axytho/FHEWHW/ThesisProjectGit/Papers/graphicsDM/oneTimePad.jpg

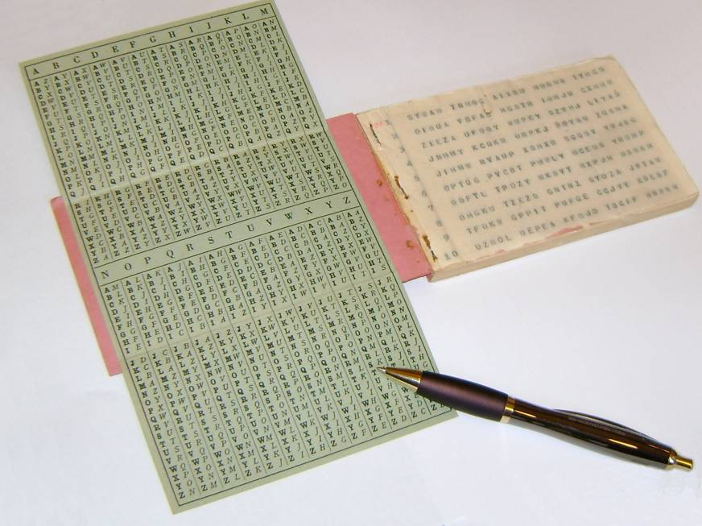
ThesisProjectGit/Papers/graphicsDM/oneTimePad.jpg
