axytho/FHEWHW/ThesisProjectGit/DraftPlanning.xlsx

 |  |  | E-mails updating the assistants are sent every week on Friday morning
 | Week | Summer holidays | Watching Simons institute lectures
1 | 39 | 2020-09-21 | Learning Microsoft SEAL
2 | 40 | 2020-09-28 | Microsoft SEAL program/ FV paper/ Pallisade lectures
3 | 41 | 2020-10-05 | FV Hardware implementation papers/ SEAL/Palisade
4 | 42 | 2020-10-12 | Further literature study and practice
5 | 43 | 2020-10-19 | Starting to work on the FPGA, learning how to program it
6 | 44 | 2020-10-26 | Literature study and decision on what to implement in hardware | Milestone: Decision on what to implement
7 | 45 | 2020-11-02 | Further literature study on scheme and start of implementation
8 | 46 | 2020-11-09 | Hardware implementation | Milestone: Planning of HW implementation and goals for different weeks
9 | 47 | 2020-11-16 | Hardware implementation
10 | 48 | 2020-11-23 | Hardware implementation
11 | 49 | 2020-11-30 | Hardware implementation
12 | 50 | 2020-12-07 | Hardware implementation
13 | 51 | 2020-12-14 | HW + Interim presentation
 | 52 | 2020-12-21 | INTERIM PRESENTATION DEADLINE | Milestone: Interim Presentation
 | 1 | 2020-12-28
 | 2 | 2021-01-04
 | 3 | 2021-01-11
 | 4 | 2021-01-18
 | 5 | 2021-01-25
 | 6 | 2021-02-01
14 | 7 | 2021-02-08 | Hardware implementation
15 | 8 | 2021-02-15 | Hardware implementation
16 | 9 | 2021-02-22 | Hardware implementation
17 | 10 | 2021-03-01 | Hardware implementation
18 | 11 | 2021-03-08 | Hardware implementation
19 | 12 | 2021-03-15 | Hardware implementation | Milestone: Finished HW implementation
20 | 13 | 2021-03-22 | Thesis write-up
21 | 14 | 2021-03-29 | Thesis write-up
22 | 15 | 2021-04-05 | Thesis write-up
23 | 16 | 2021-04-12 | Thesis write-up
24 | 17 | 2021-04-19 | Thesis write-up | Milestone: Finished Thesis
25 | 18 | 2021-04-26 | Article write-up
26 | 19 | 2021-05-03 | Article write-up | Milestone: Finished Article
 | 20 | 2021-05-10 | Further optimizations if possible and thesis write-up
 | 21 | 2021-05-17 | Further optimizations if possible and thesis write-up
 | 22 | 2021-05-24 | Further optimizations if possible and thesis write-up | Milestone: Thesis spell checked/ corrected and further optimizations done
 | 23 | 2021-05-31 | THESIS DEADLINE
 |  |  |  | Milestone: Final Presentation
