axytho/FHEWHW/ThesisProjectGit/2022Work/Capture.PNG

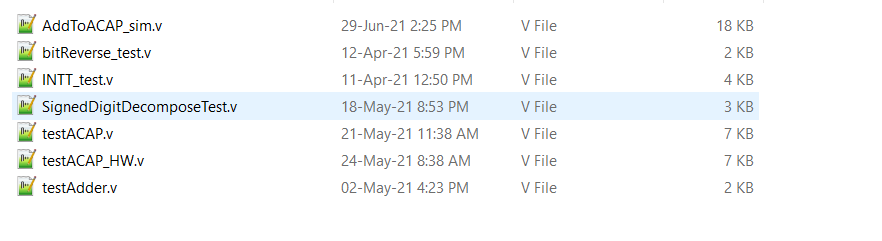
ThesisProjectGit/2022Work/Capture.PNG
