axytho/FHEWHW/ThesisProjectGit/blockDiagram/leftSide.PNG

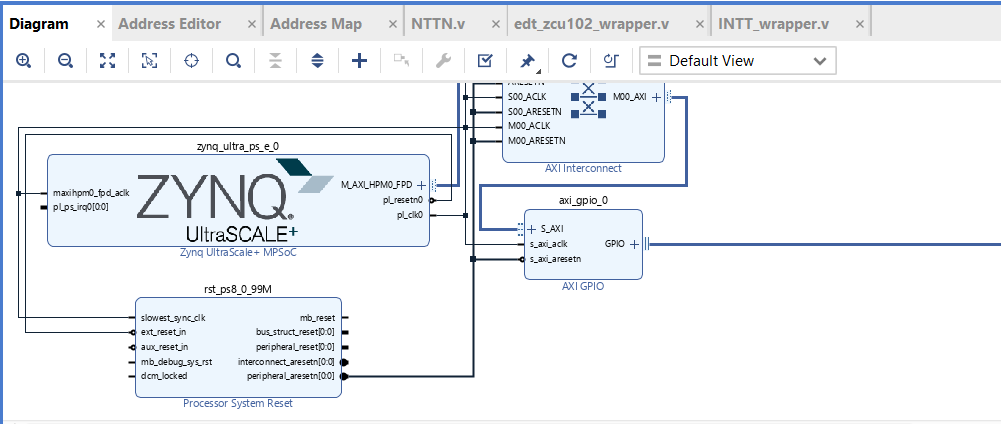
ThesisProjectGit/blockDiagram/leftSide.PNG
