axytho/FHEWHW/ThesisProjectGit/blockDiagram/RightSide.PNG

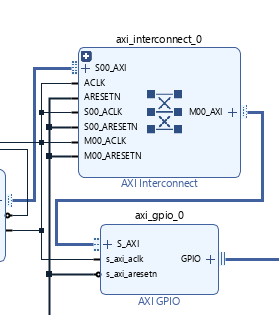
ThesisProjectGit/blockDiagram/RightSide.PNG
