axytho/FHEWHW/ThesisProjectGit/Papers/graphicsDM/Accumulation.PNG

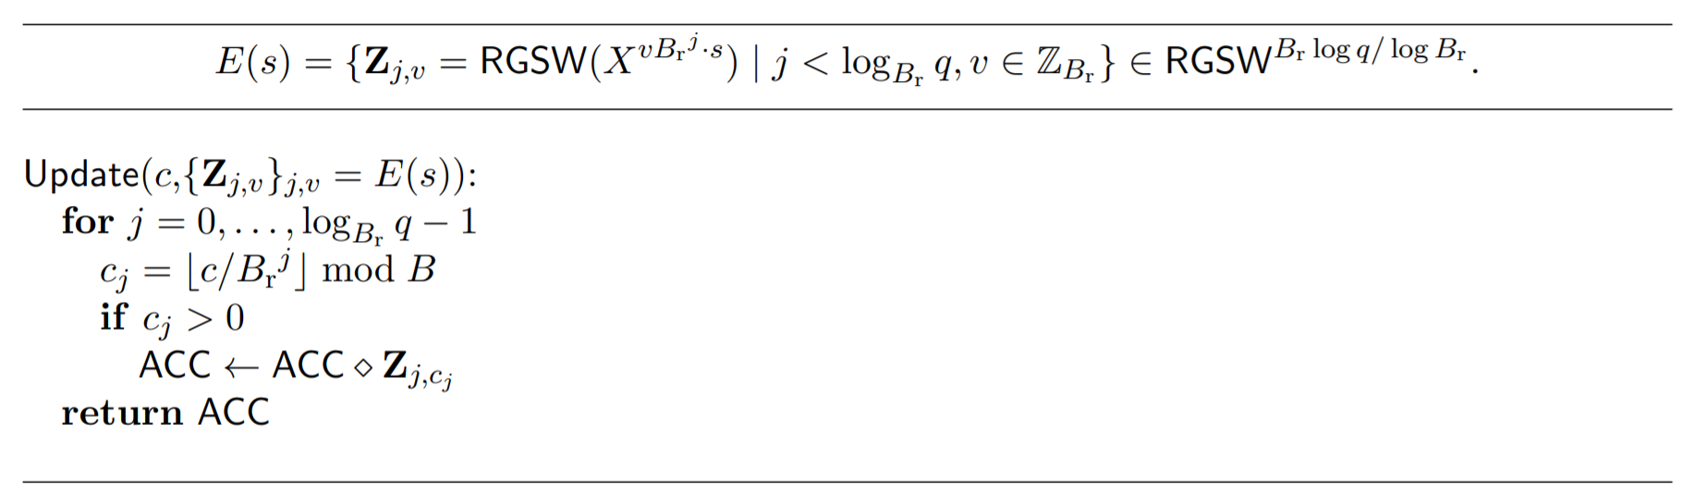
ThesisProjectGit/Papers/graphicsDM/Accumulation.PNG
