axytho/FHEWHW/ThesisProjectGit/Papers/graphicsDM/boxInsideABox.png

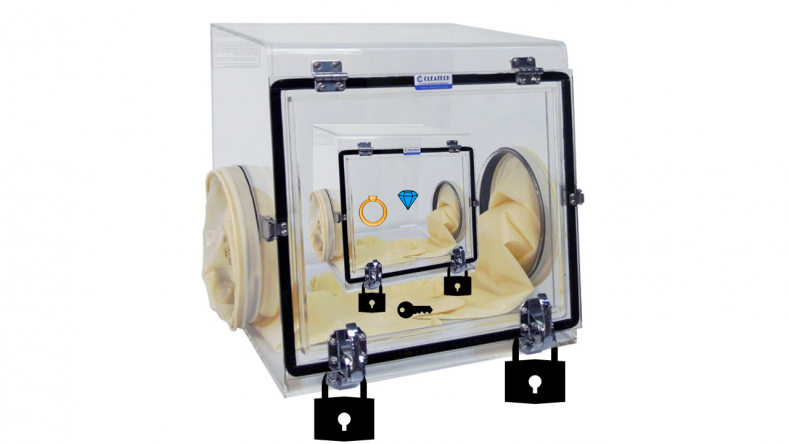
ThesisProjectGit/Papers/graphicsDM/boxInsideABox.png
