axytho/FHEWHW/ThesisProjectGit/Papers/graphicsDM/CooleyTukey.PNG

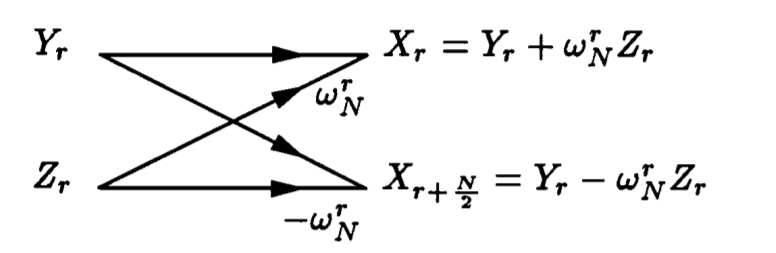
ThesisProjectGit/Papers/graphicsDM/CooleyTukey.PNG
