axytho/FHEWHW/ThesisProjectGit/Papers/graphicsDM/ElevenClockCycleBRAM.PNG

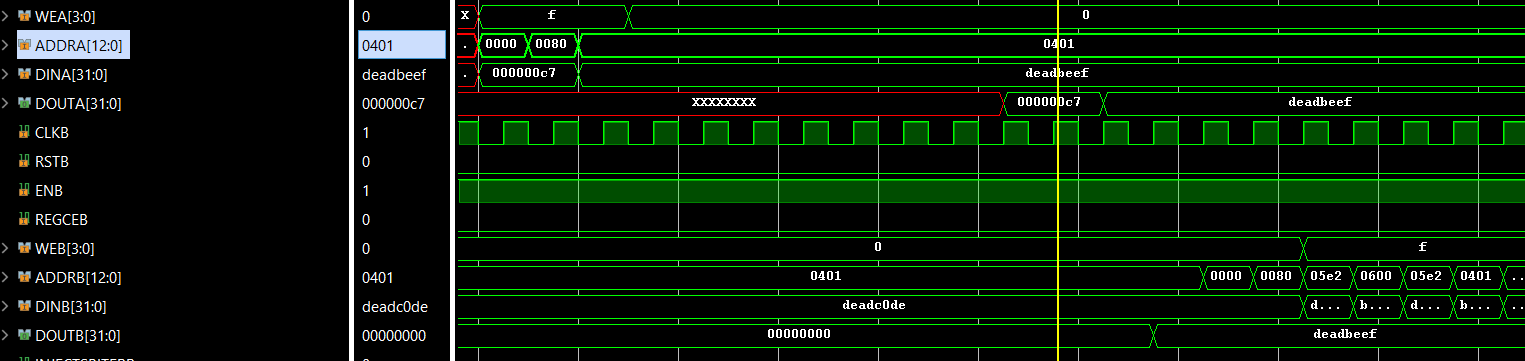
ThesisProjectGit/Papers/graphicsDM/ElevenClockCycleBRAM.PNG
