axytho/FHEWHW/ThesisProjectGit/Papers/graphicsDM/FHEWflowchart.png

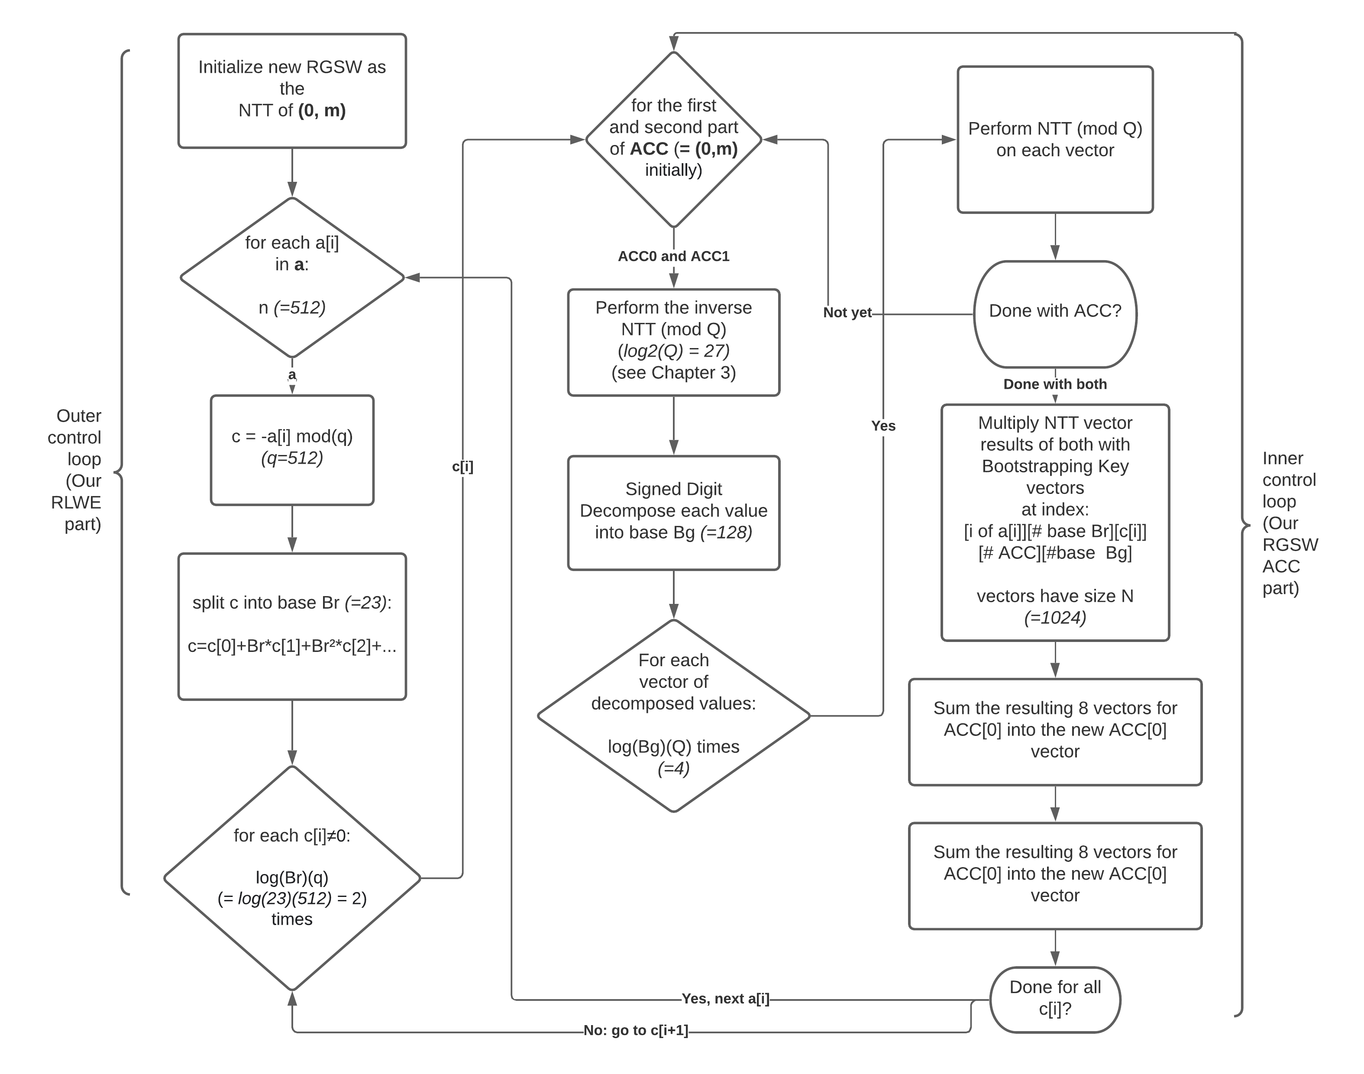
ThesisProjectGit/Papers/graphicsDM/FHEWflowchart.png
