axytho/FHEWHW/ThesisProjectGit/Papers/graphicsDM/GentlemanSande.PNG

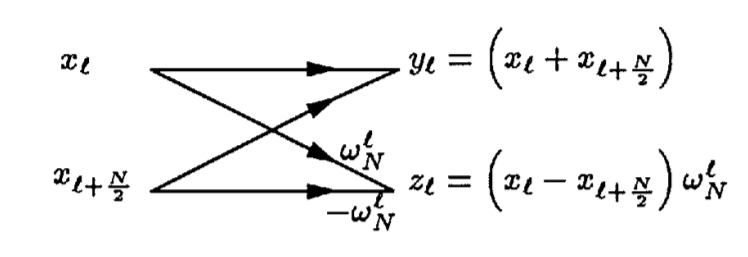
ThesisProjectGit/Papers/graphicsDM/GentlemanSande.PNG
