axytho/FHEWHW/ThesisProjectGit/Papers/graphicsDM/InitializationExtraction.PNG

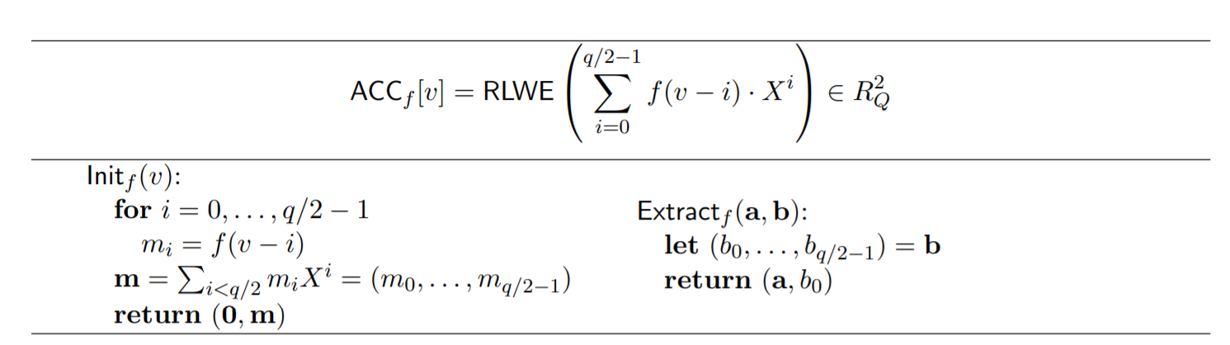
ThesisProjectGit/Papers/graphicsDM/InitializationExtraction.PNG
