axytho/FHEWHW/ThesisProjectGit/Papers/graphicsDM/MERTINTT.png

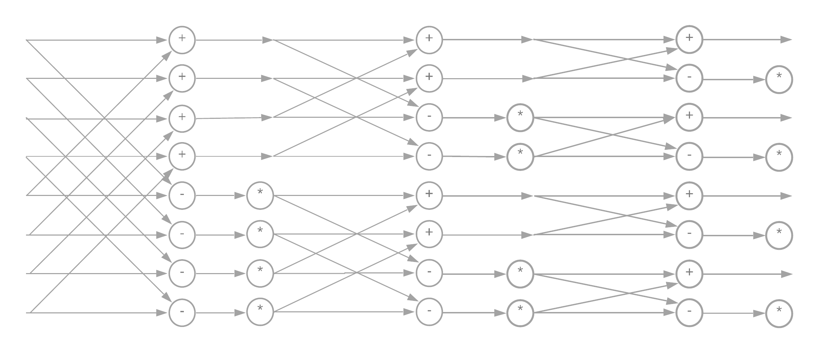
ThesisProjectGit/Papers/graphicsDM/MERTINTT.png
