axytho/FHEWHW/ThesisProjectGit/Papers/graphicsDM/Picture1.png

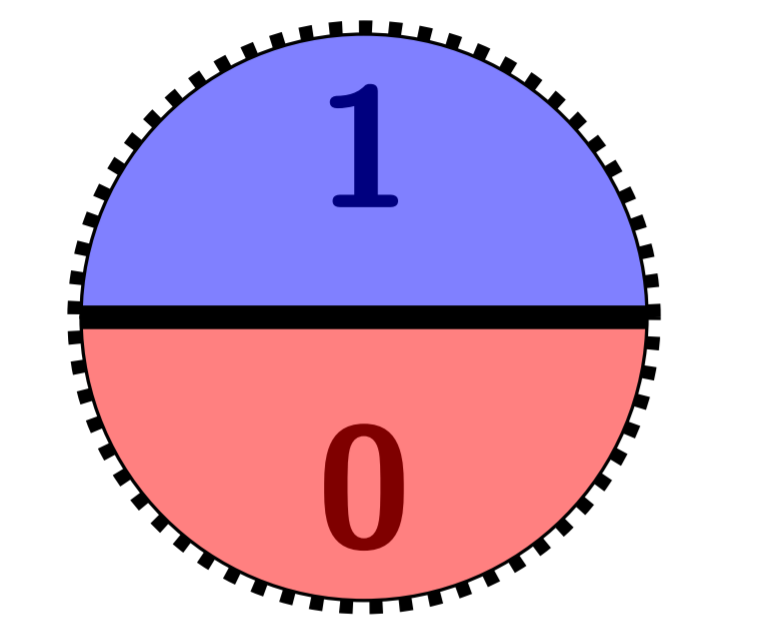
ThesisProjectGit/Papers/graphicsDM/Picture1.png
