axytho/FHEWHW/ThesisProjectGit/Papers/graphicsDM/Picture2.png

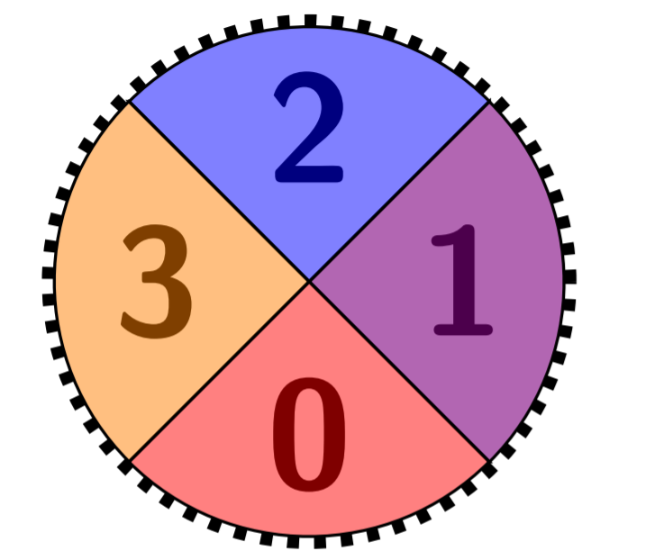
ThesisProjectGit/Papers/graphicsDM/Picture2.png
