axytho/FHEWHW/ThesisProjectGit/Papers/graphicsDM/Picture2half.PNG

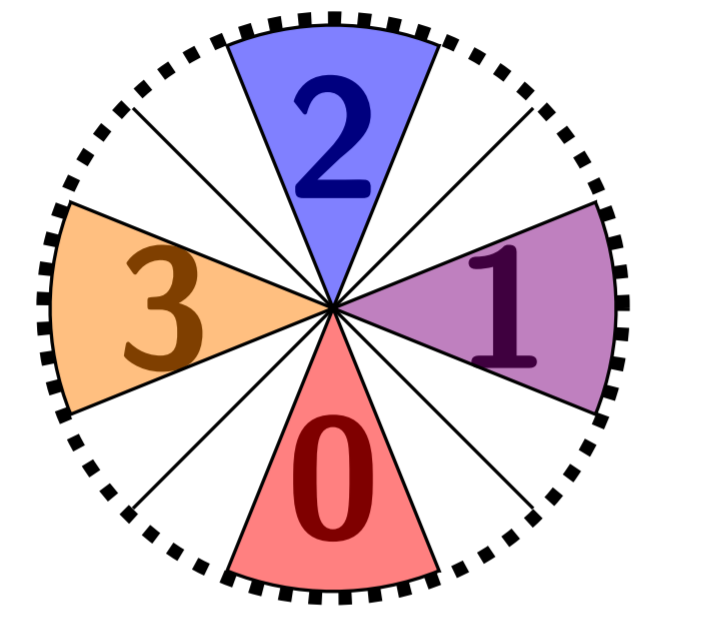
ThesisProjectGit/Papers/graphicsDM/Picture2half.PNG
