axytho/FHEWHW/ThesisProjectGit/Papers/graphicsDM/Picture3.png

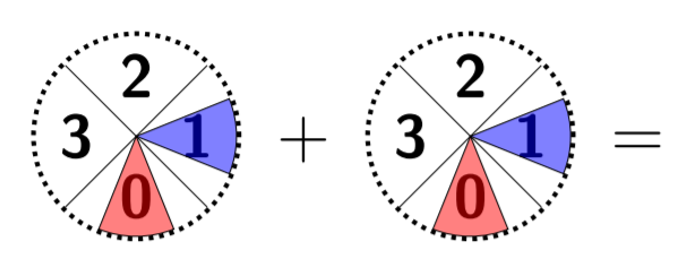
ThesisProjectGit/Papers/graphicsDM/Picture3.png
