axytho/FHEWHW/ThesisProjectGit/Papers/graphicsDM/Picture5.png

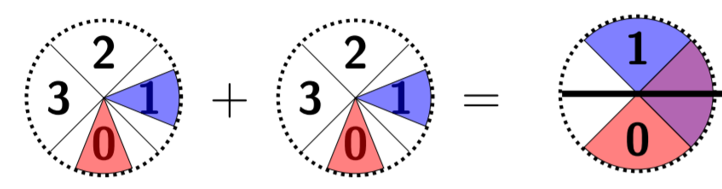
ThesisProjectGit/Papers/graphicsDM/Picture5.png
