axytho/FHEWHW/ThesisProjectGit/TechnicalIssueScreenshots/schematicZCU102.jpg

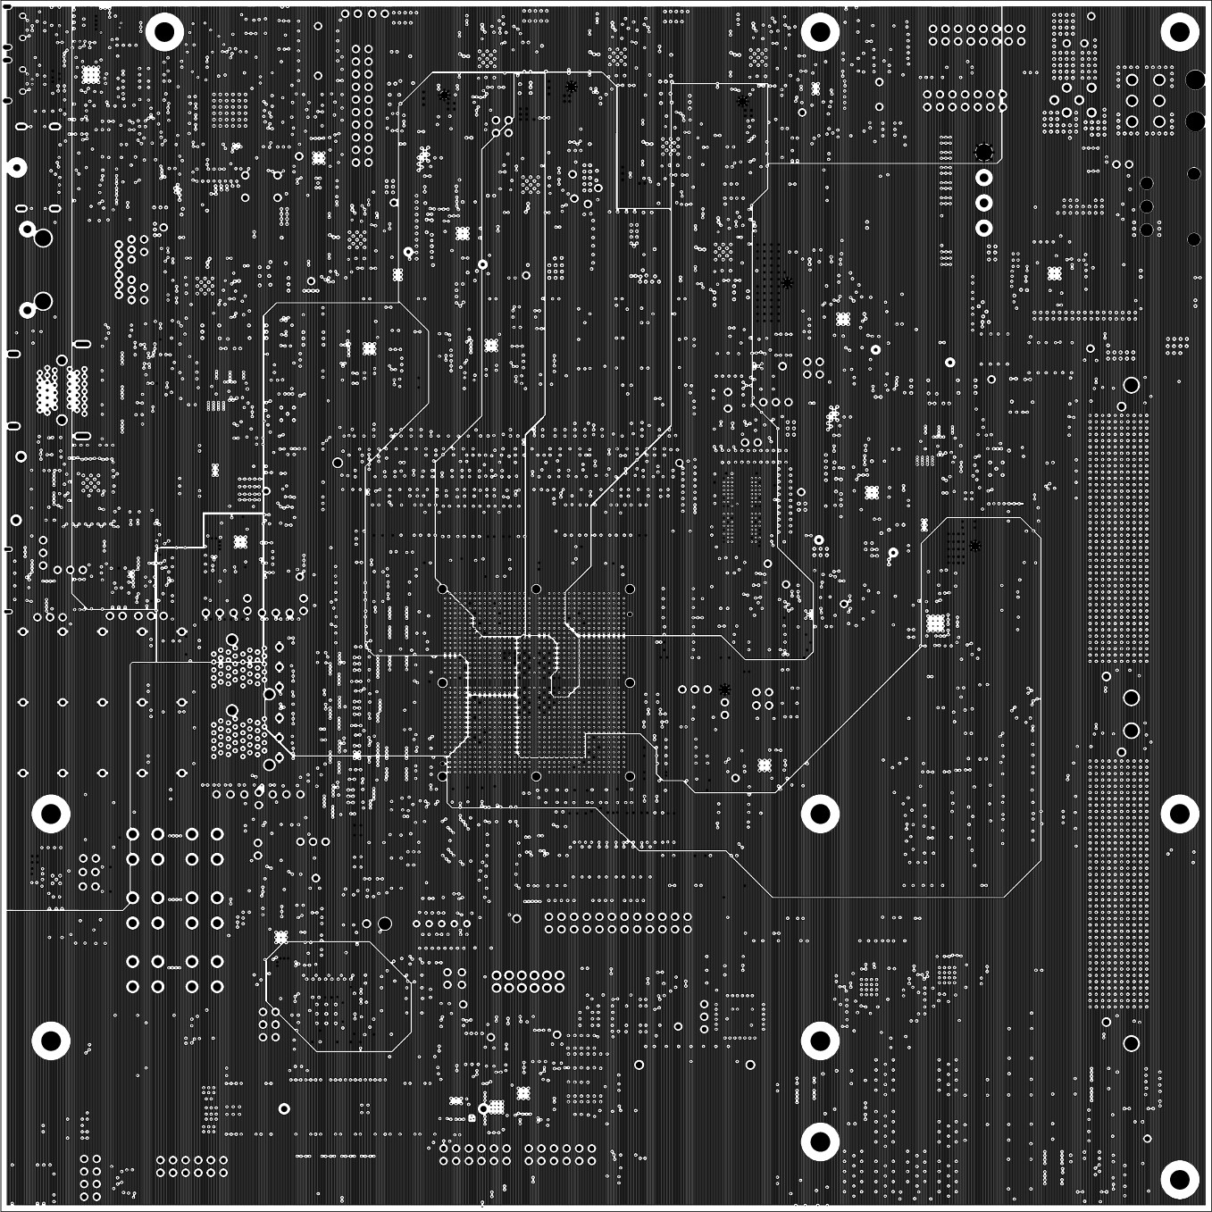
ThesisProjectGit/TechnicalIssueScreenshots/schematicZCU102.jpg
