axytho/FHEWHW/ThesisProjectGit/waveForms/NTT2DetailLeft.PNG

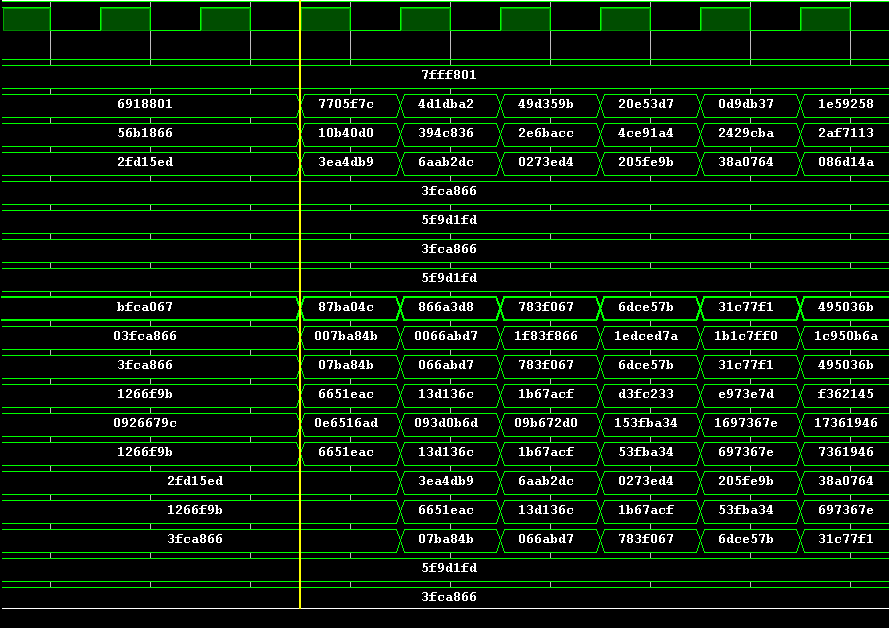
ThesisProjectGit/waveForms/NTT2DetailLeft.PNG
