axytho/FHEWHW/ThesisProjectGit/waveForms/NTT2DetailMiddle.PNG

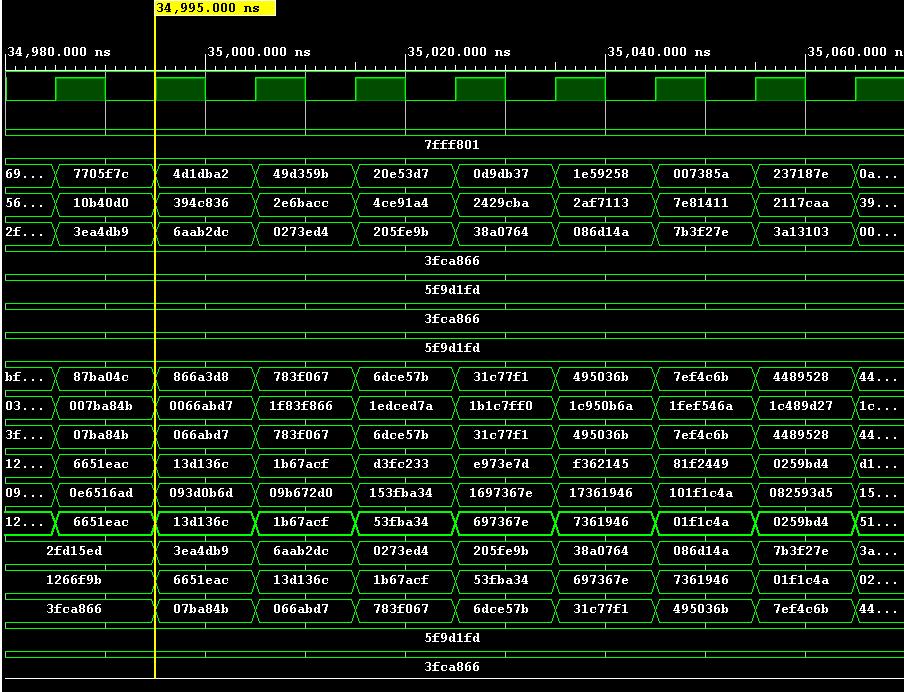
ThesisProjectGit/waveForms/NTT2DetailMiddle.PNG
