axytho/FHEWHW/ThesisProjectGit/waveForms/NTT2DetailRight.PNG

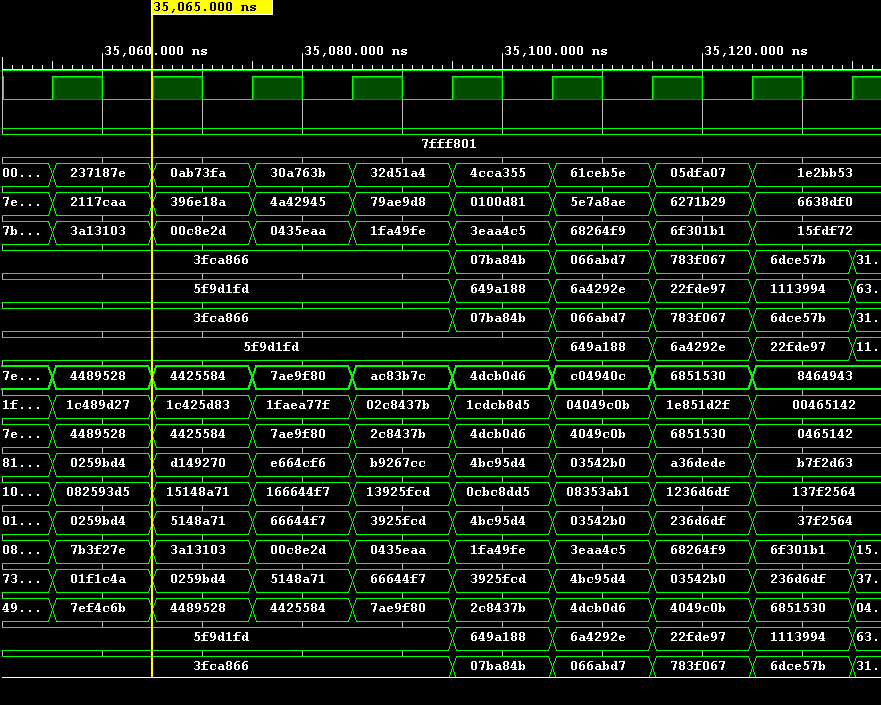
ThesisProjectGit/waveForms/NTT2DetailRight.PNG
