axytho/FHEWHW/ThesisProjectGit/TechnicalIssueScreenshots/Blockdiagram2.PNG

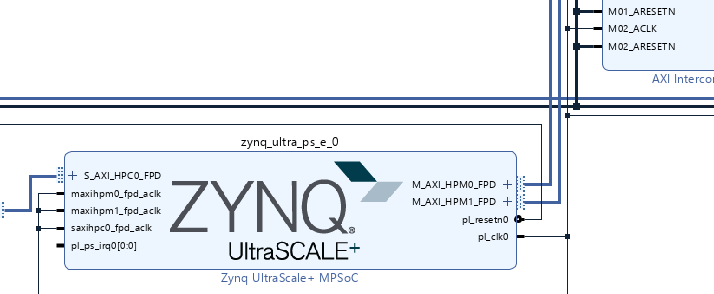
ThesisProjectGit/TechnicalIssueScreenshots/Blockdiagram2.PNG
