axytho/FHEWHW/ThesisProjectGit/TechnicalIssueScreenshots/Blockdiagram3.PNG

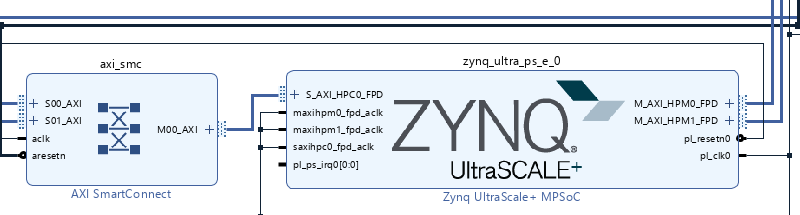
ThesisProjectGit/TechnicalIssueScreenshots/Blockdiagram3.PNG
