axytho/FHEWHW/ThesisProjectGit/TechnicalIssueScreenshots/Blockdiagram.PNG

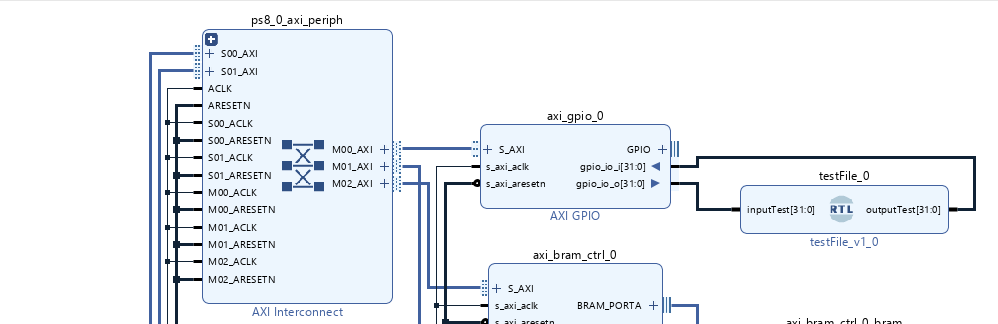
ThesisProjectGit/TechnicalIssueScreenshots/Blockdiagram.PNG
