axytho/FHEWHW/ThesisProjectGit/TechnicalIssueScreenshots/Cmd.PNG

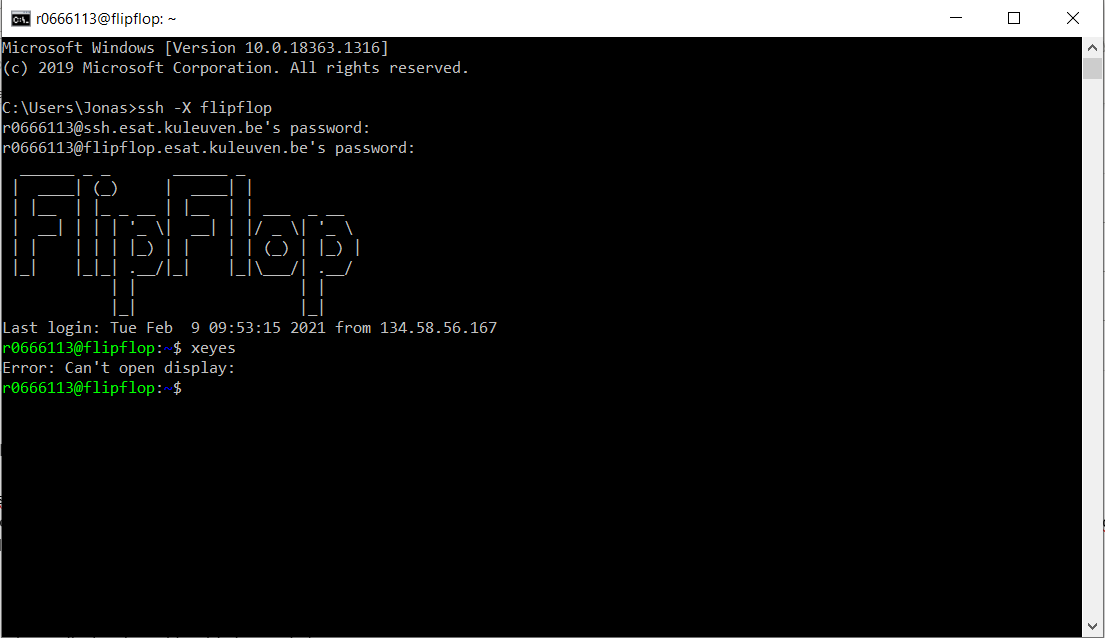
ThesisProjectGit/TechnicalIssueScreenshots/Cmd.PNG
