axytho/FHEWHW/ThesisProjectGit/TechnicalIssueScreenshots/drawing.jpg

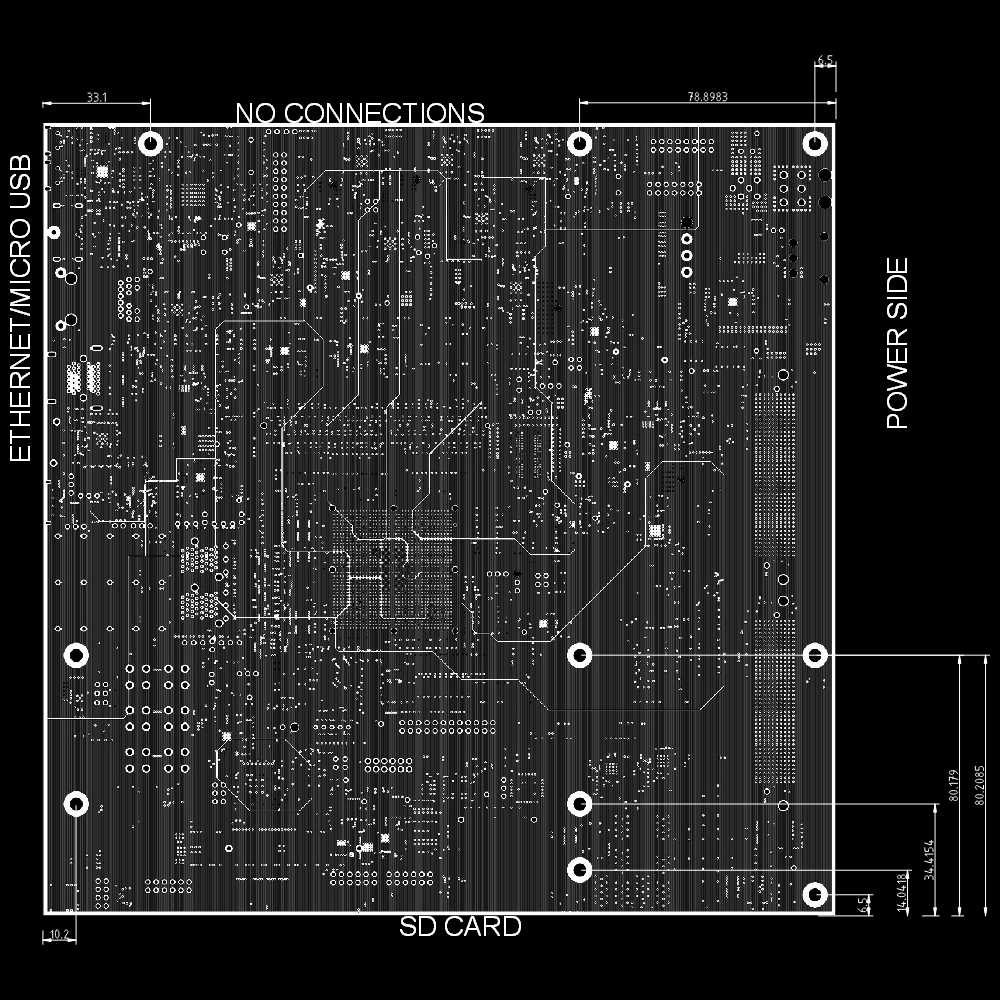
ThesisProjectGit/TechnicalIssueScreenshots/drawing.jpg
