axytho/FHEWHW/ThesisProjectGit/Papers/FirstTwoChapters.pdf

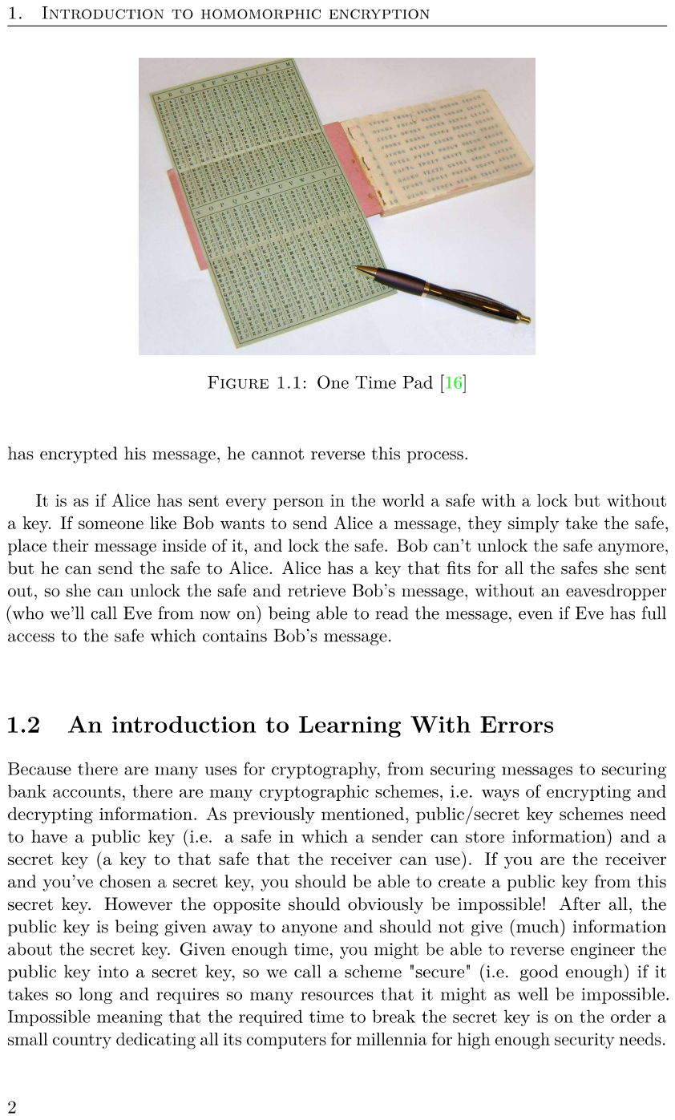
[picture p122: page 2]

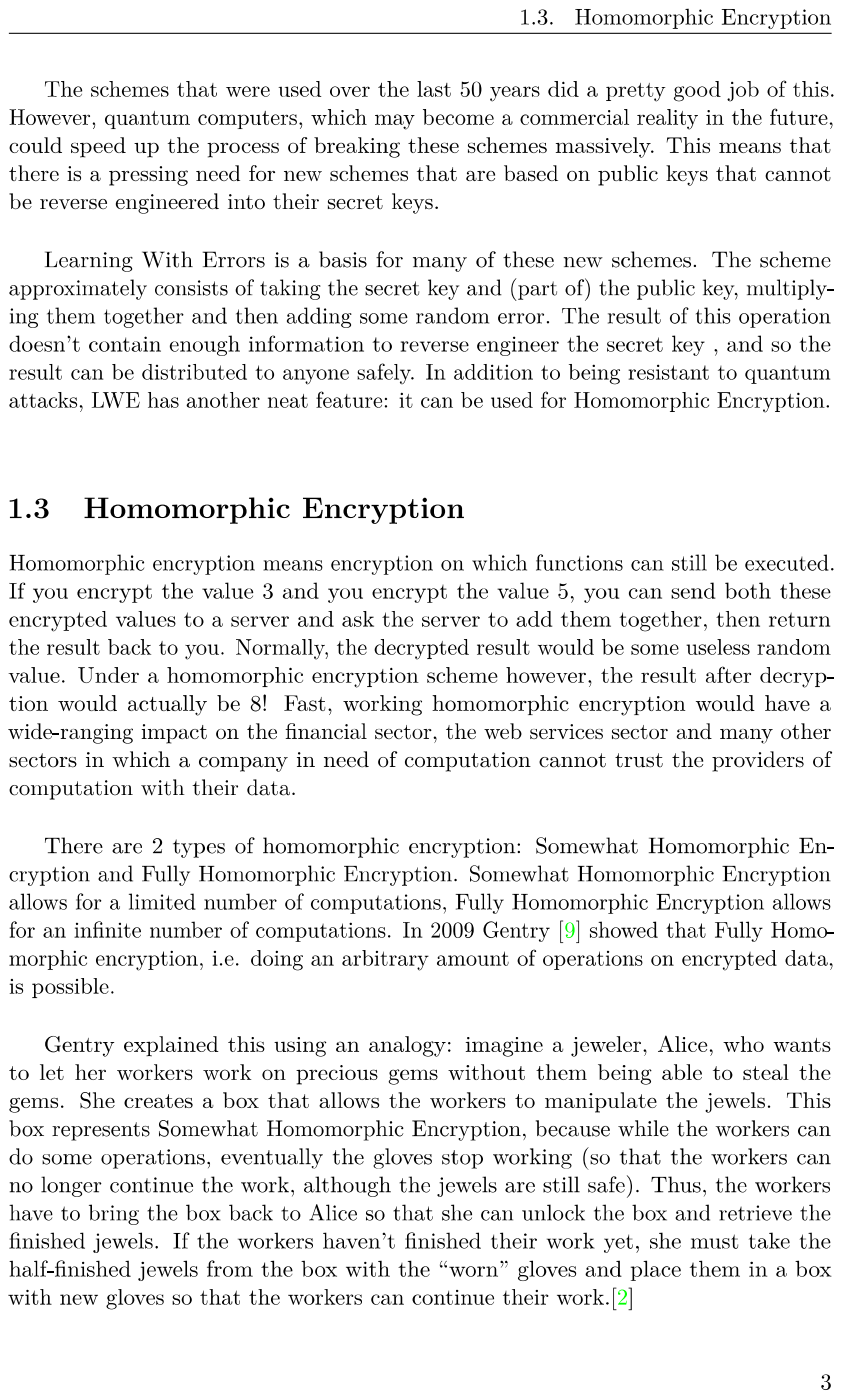
[picture p123: page 3]

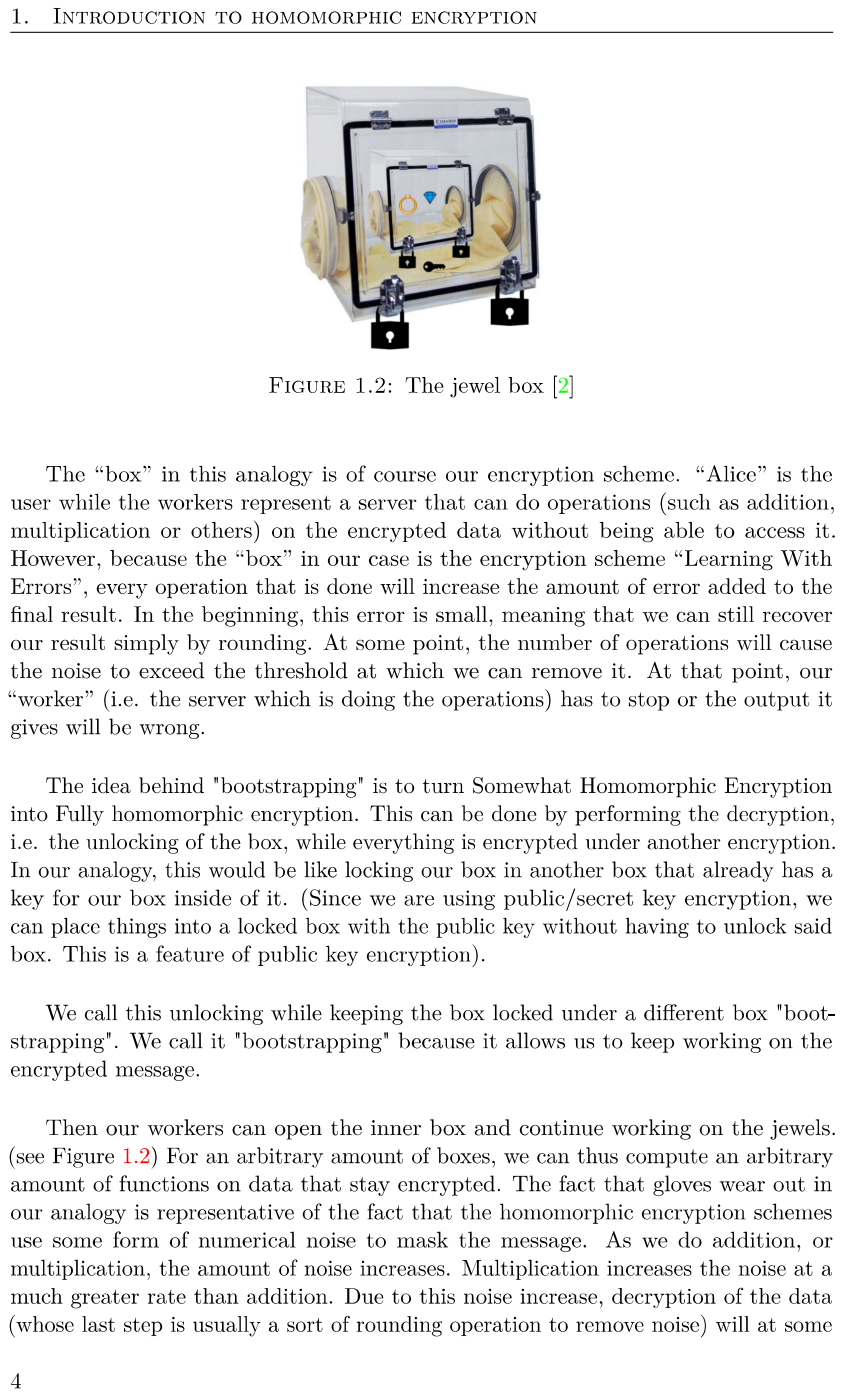
[picture p124: page 4]

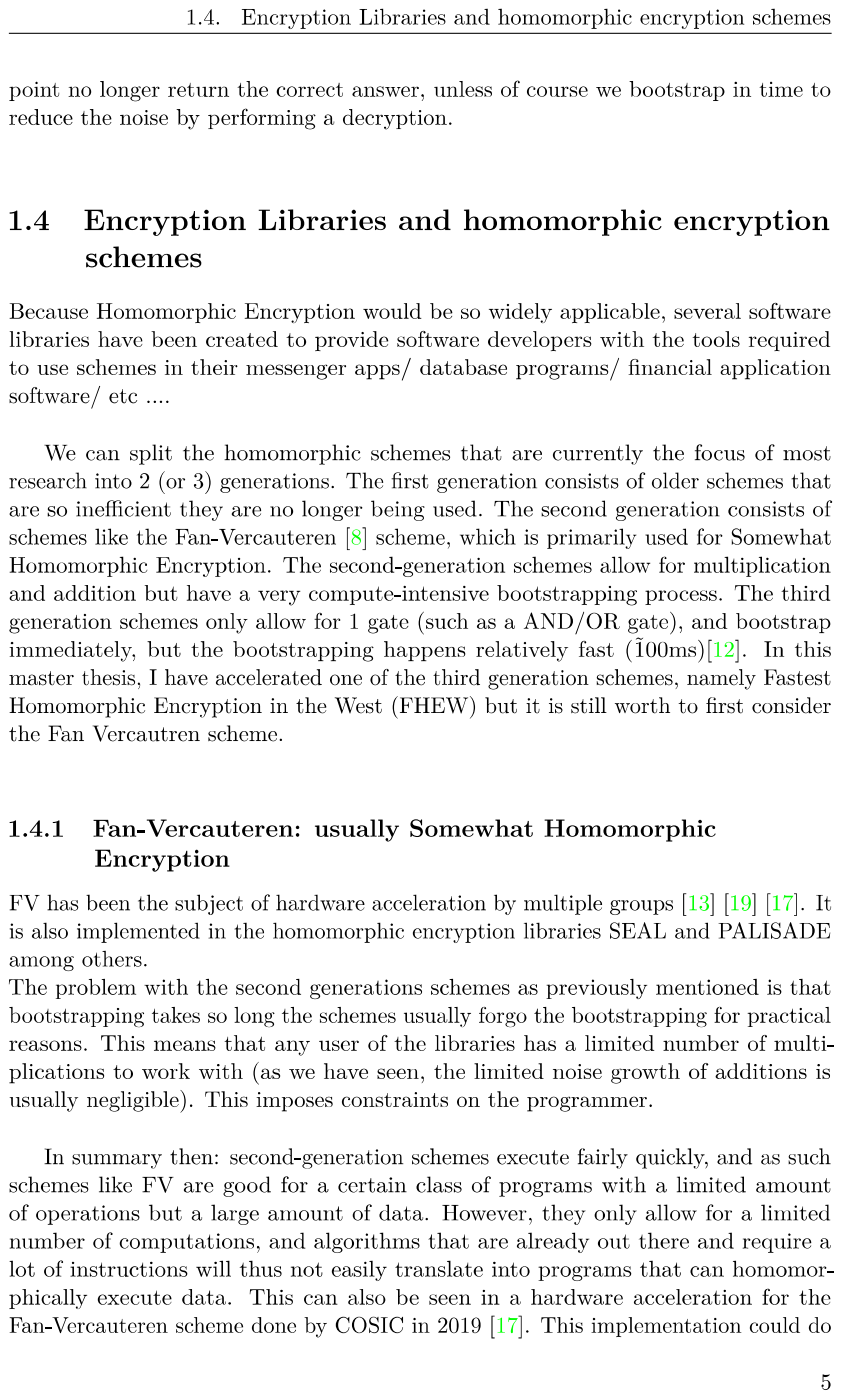
[picture p125: page 5]

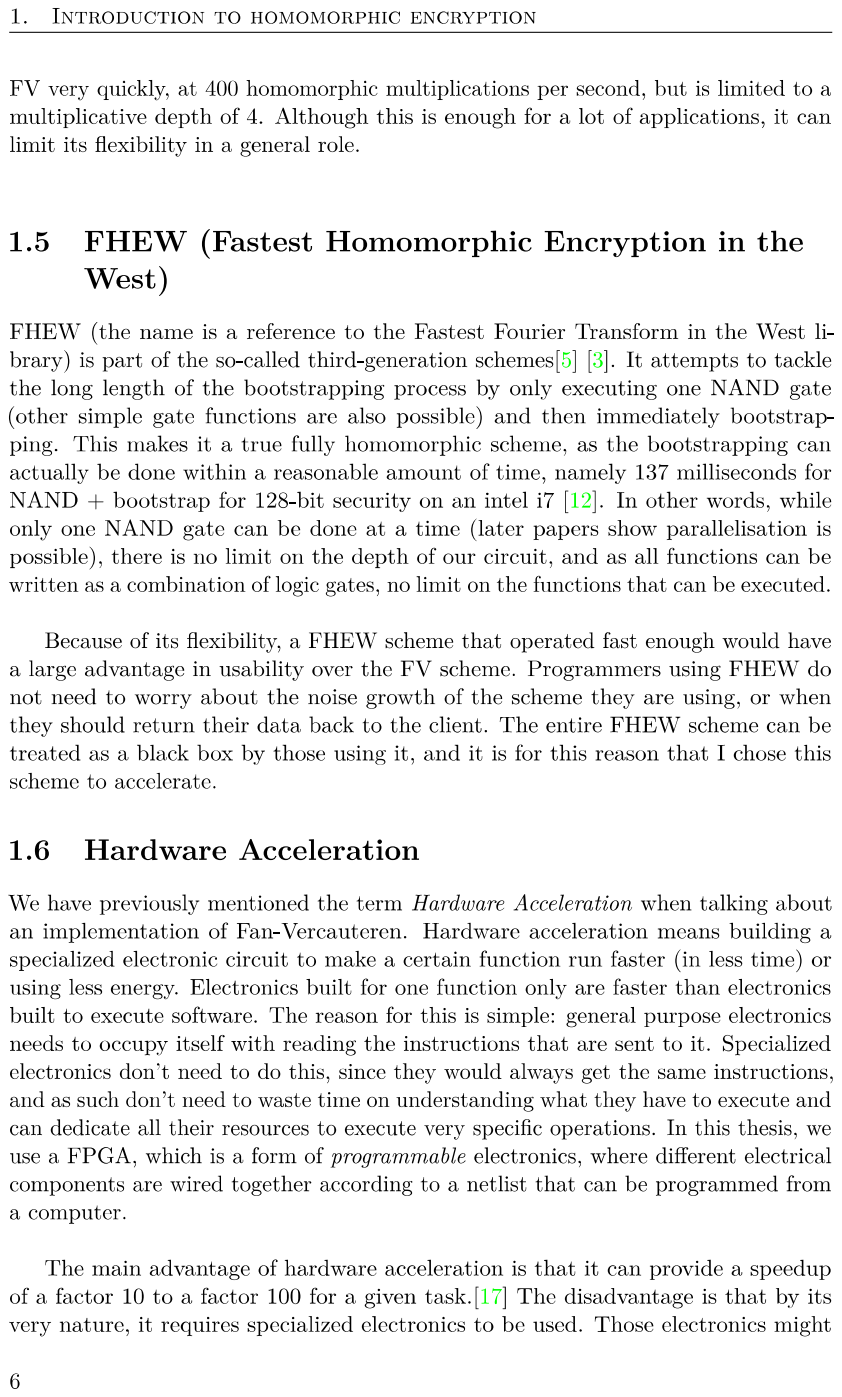
[picture p126: page 6]

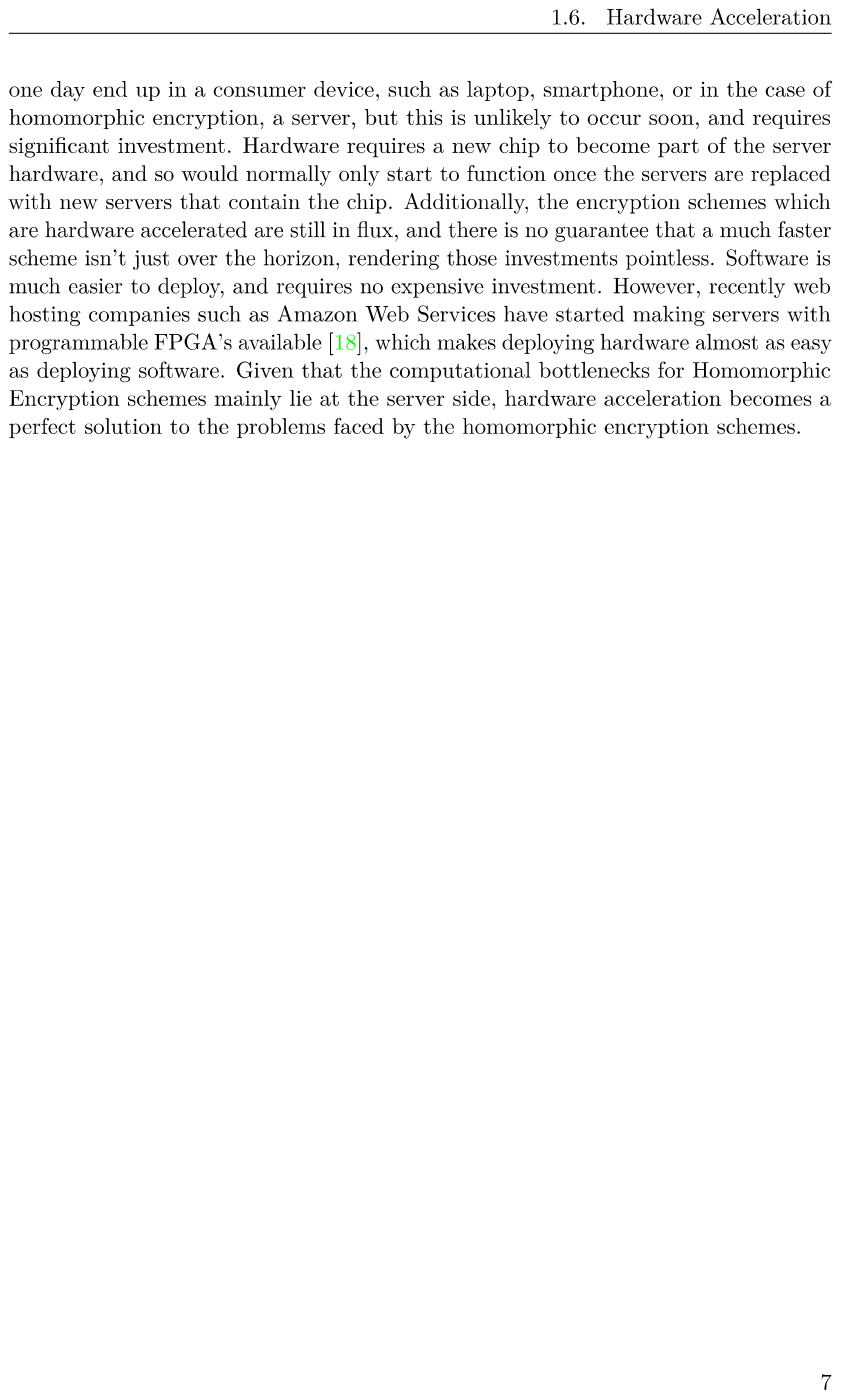
[picture p127: page 7]

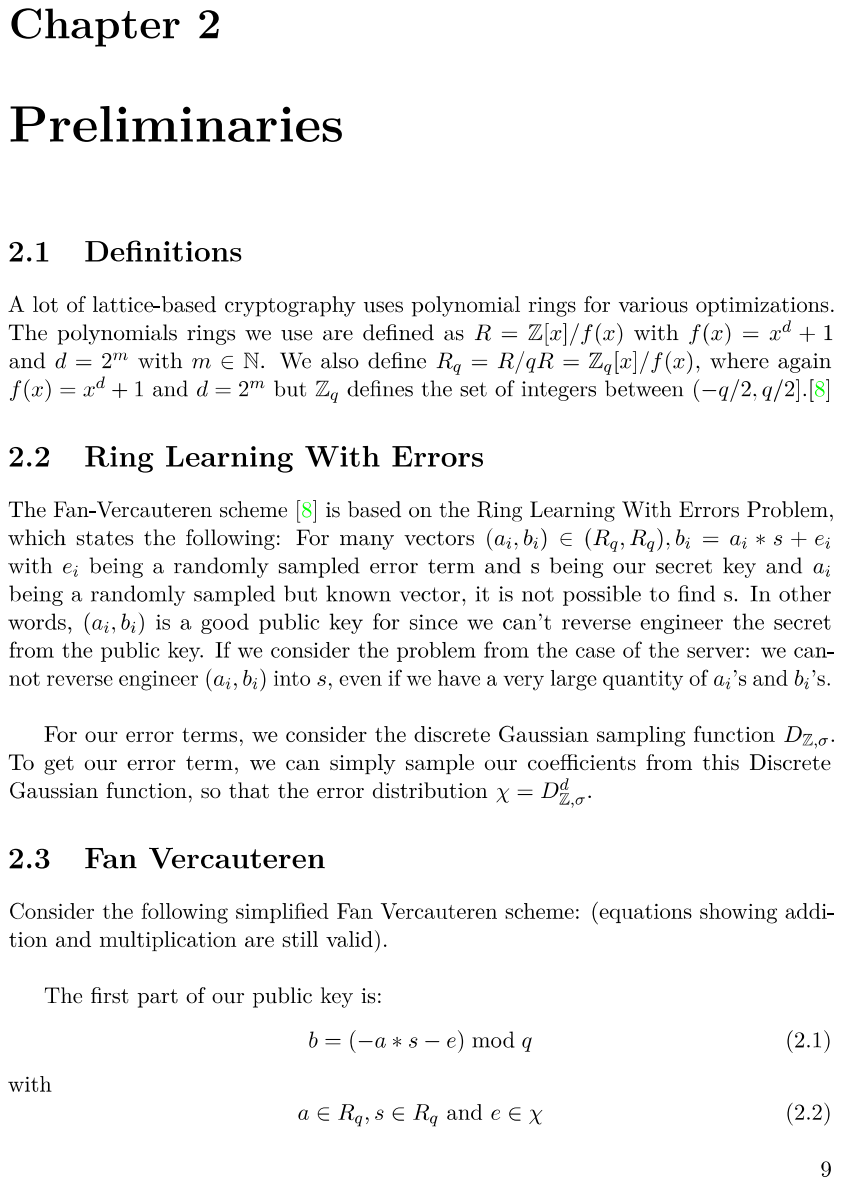
[picture p128: page 9]

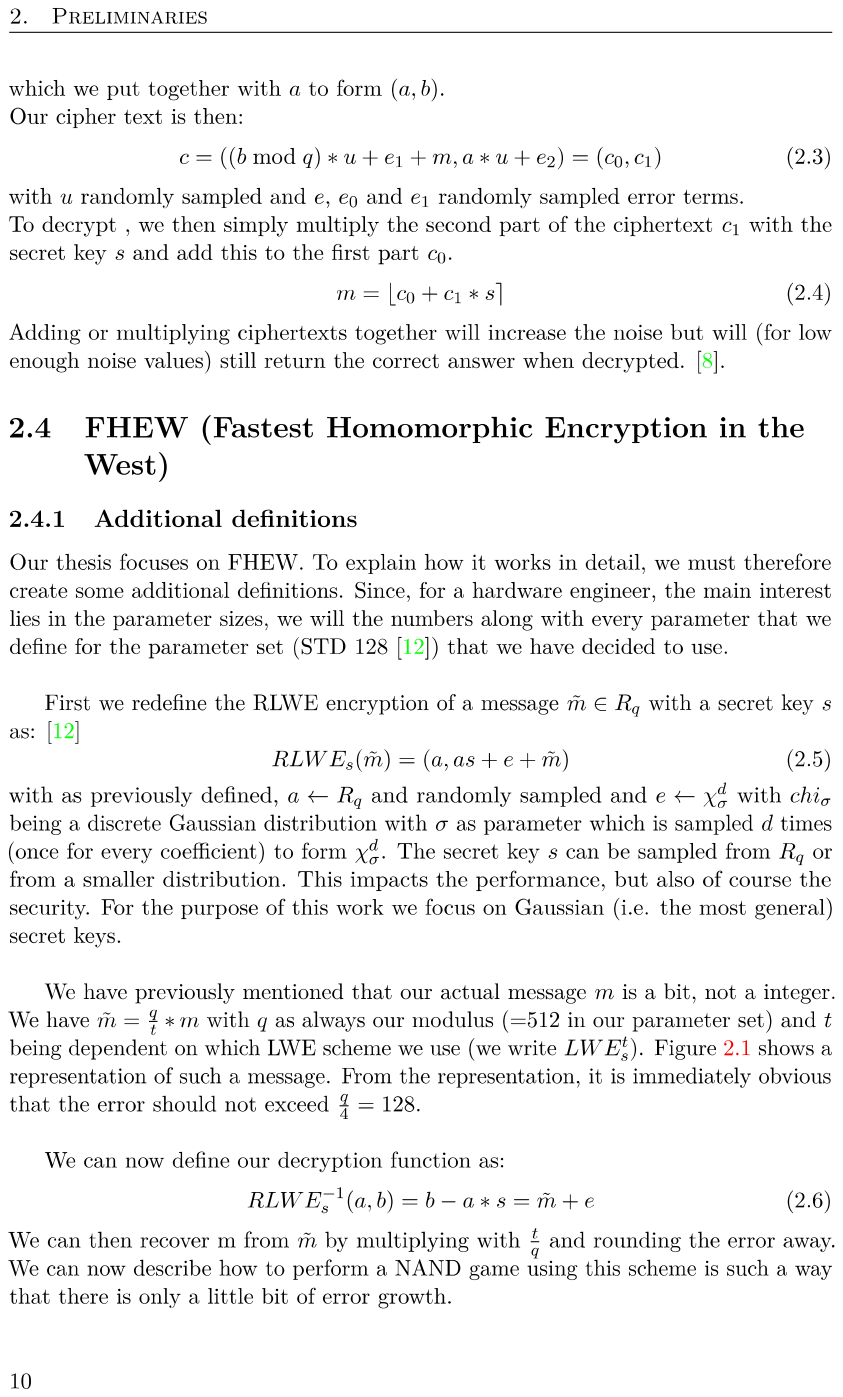
[picture p129: page 10]

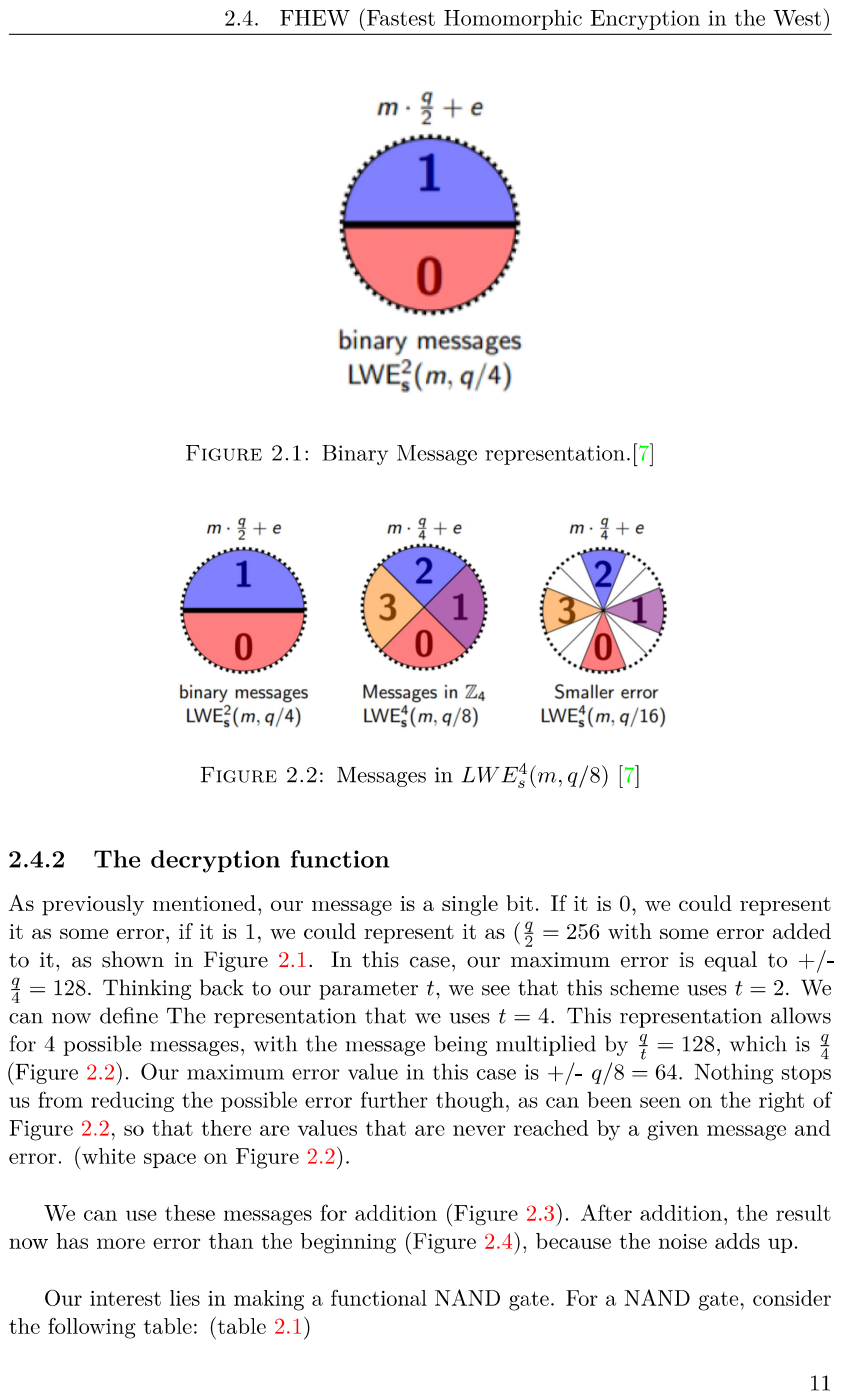
[picture p130: page 11]

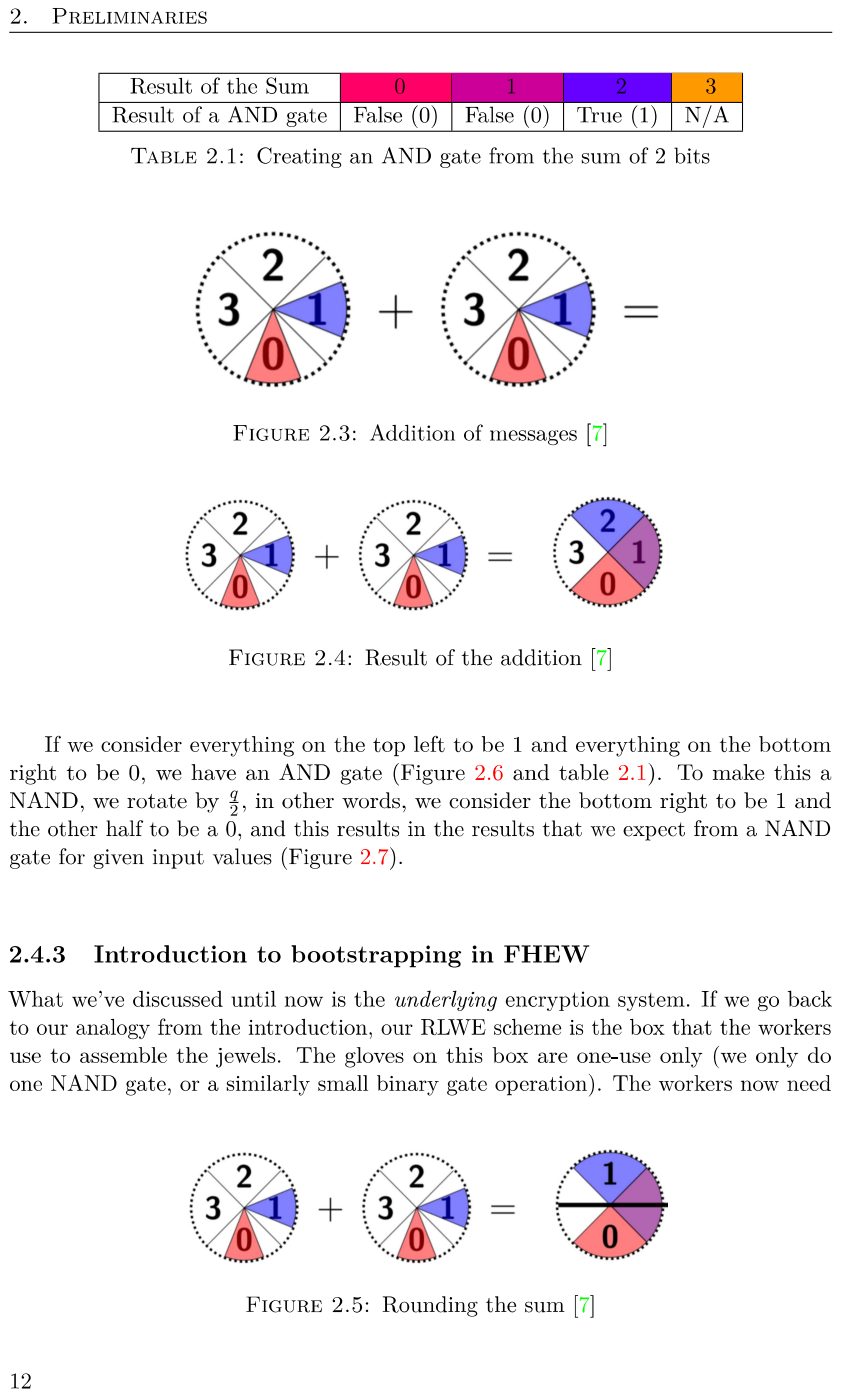
[picture p131: page 12]

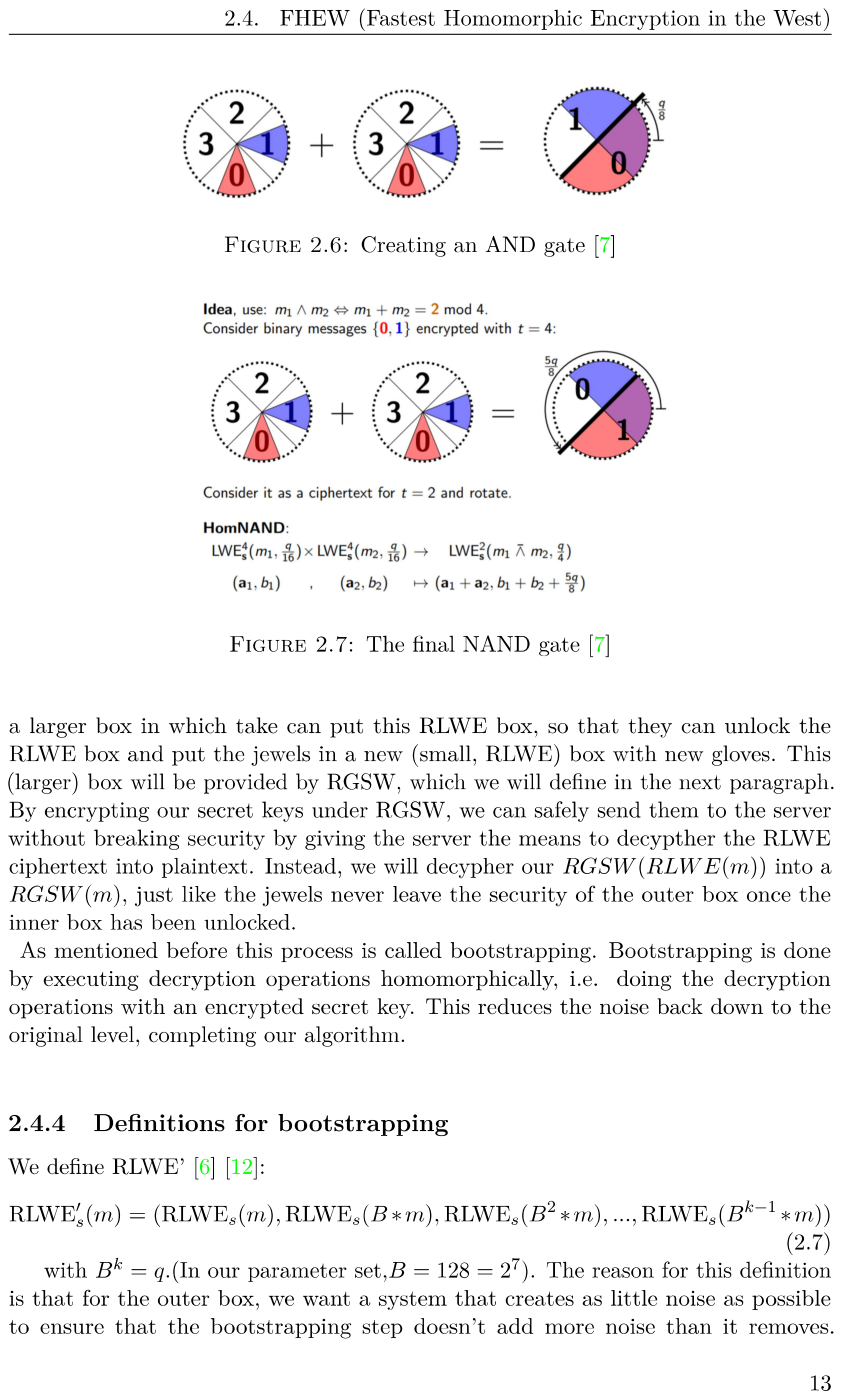
[picture p132: page 13]

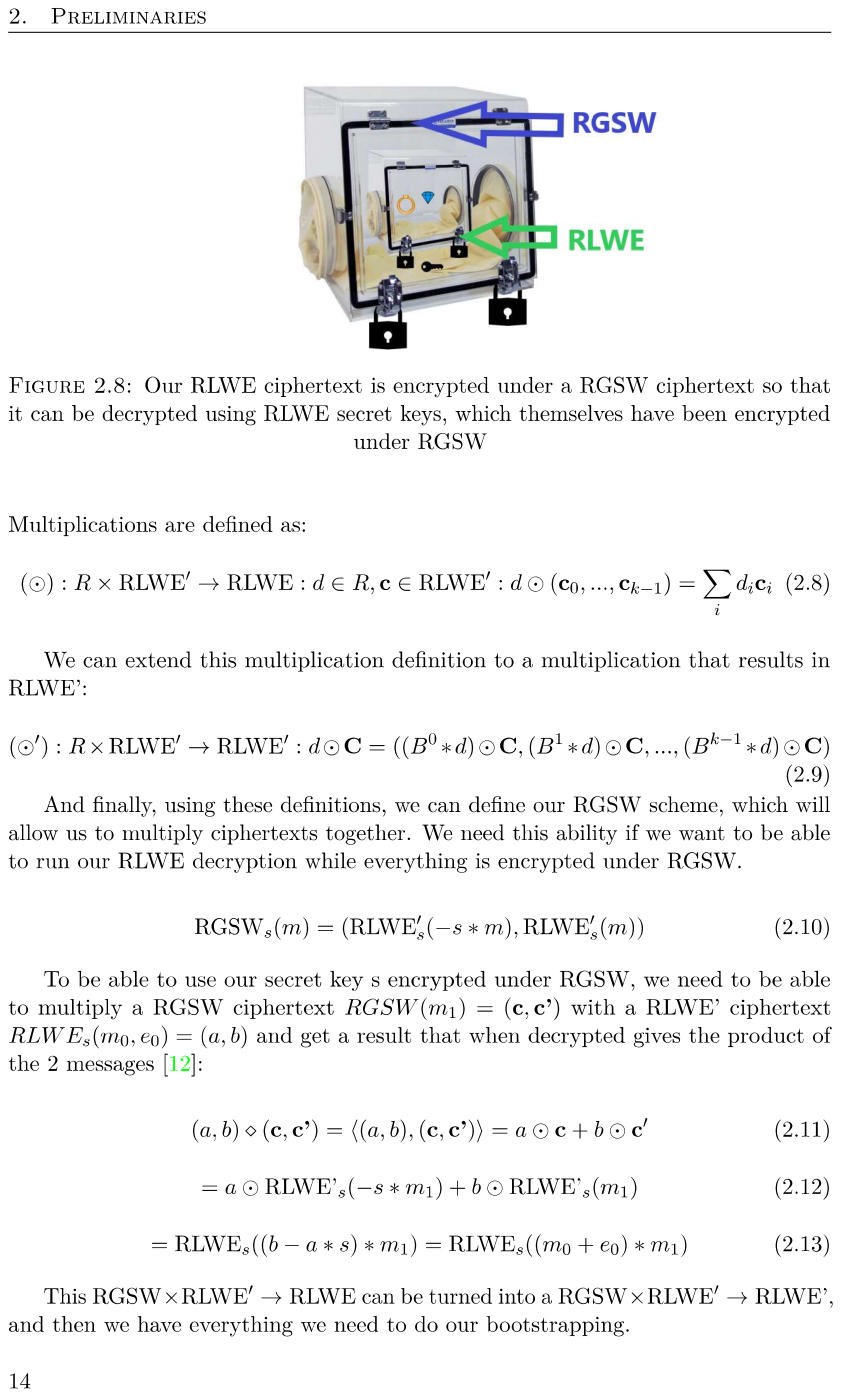
[picture p133: page 14]

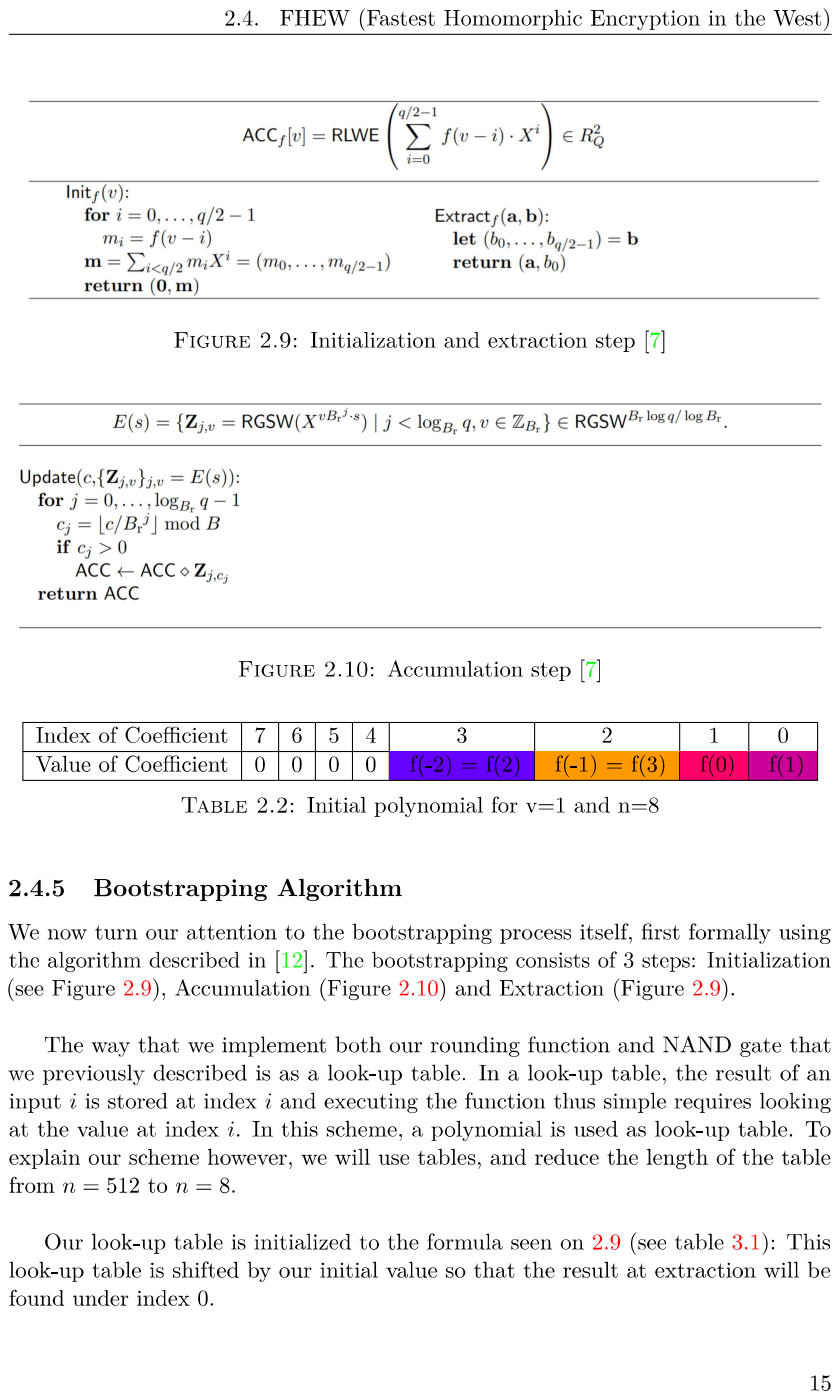
[picture p134: page 15]

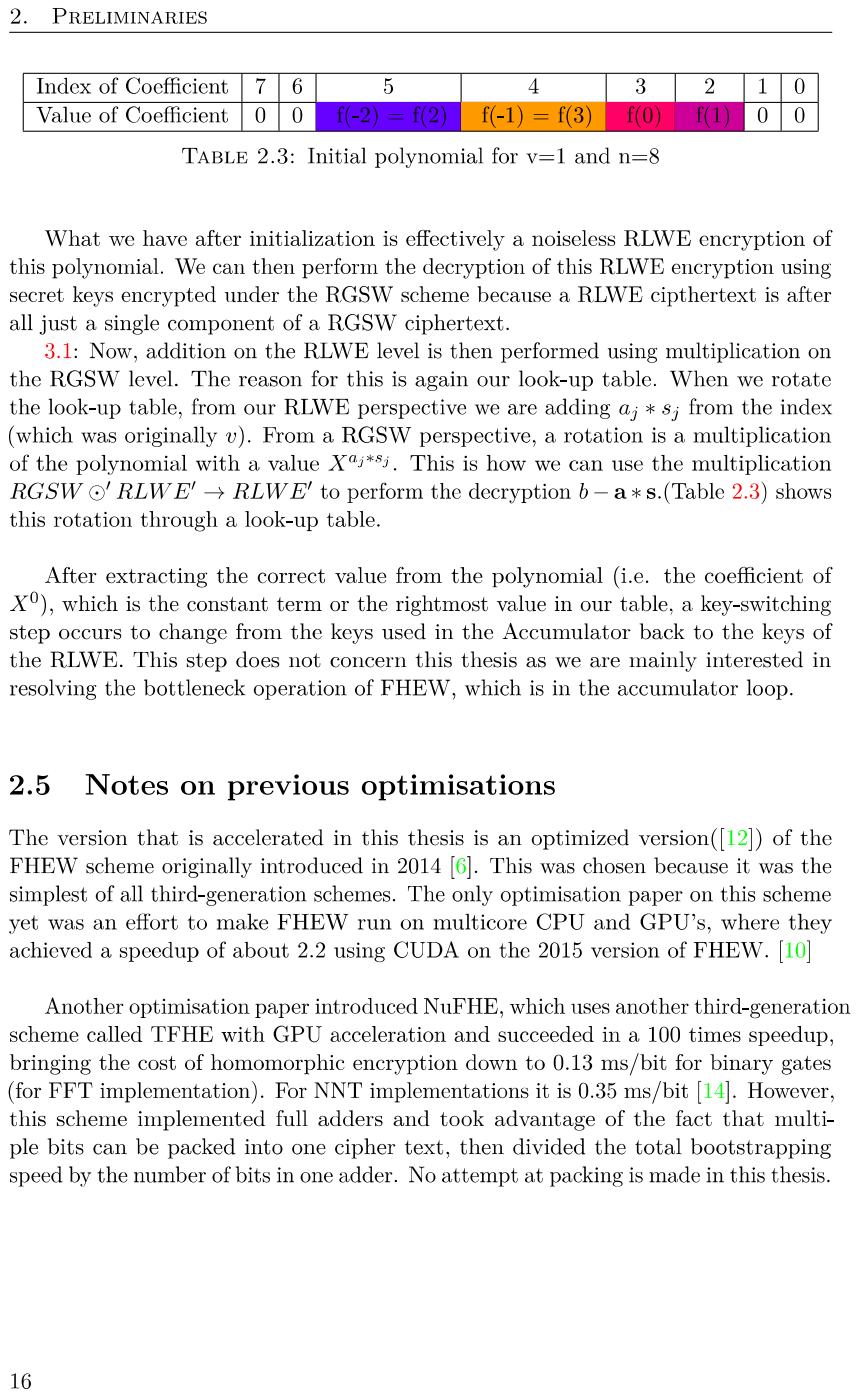
[picture p135: page 16]
