axytho/FHEWHW/ThesisProjectGit/Papers/graphicsDM/FHEWcircuit.pdf

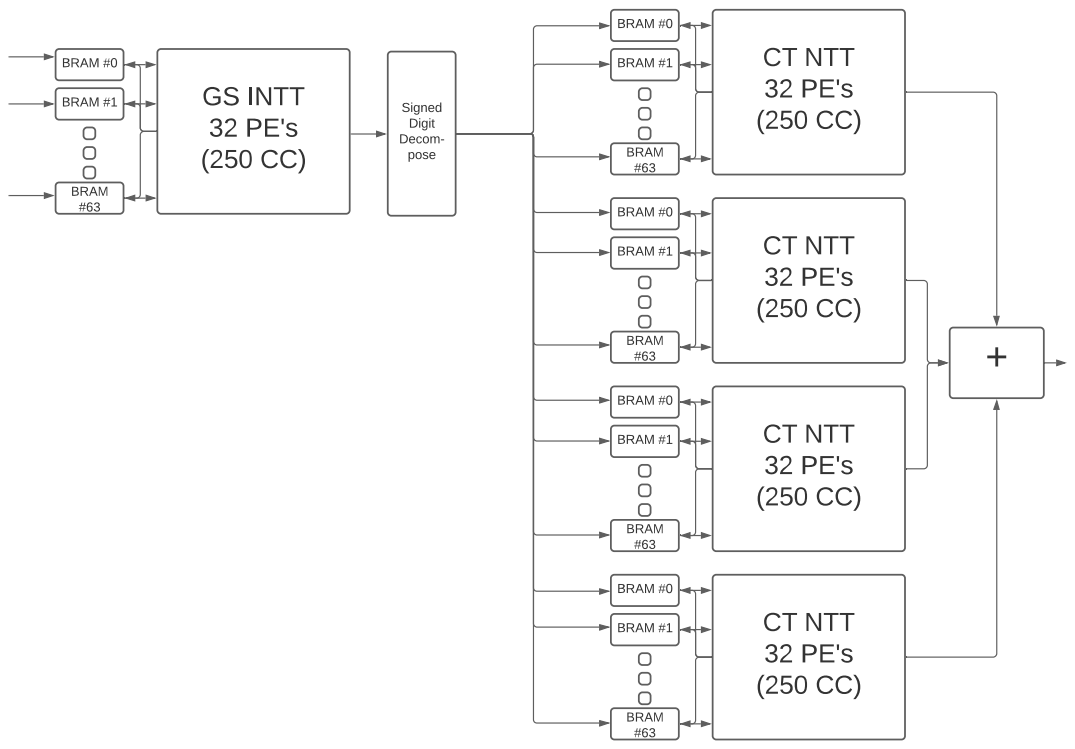
[picture p136: page 1]
Sig; d Digit
