axytho/FHEWHW/ThesisProjectGit/Papers/graphicsDM/FHEWflowchart.pdf

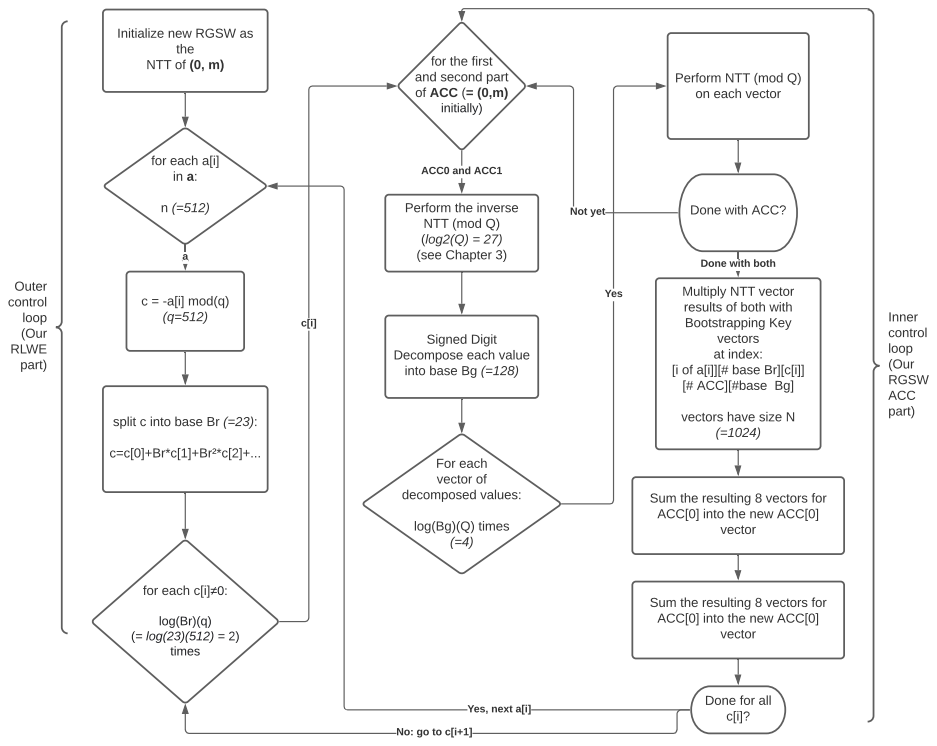
[picture p137: page 1]
Initializ; plit; fir; ) initially); Sig; Digit; alu; wit; ultiply; ult; pin; x: [i of a[i]][# base; ultin; C[0] vector

ol loop (Our

ol loop (Our RGSW ACC part)
r][c[i]] [# ACC][#base Bg] vectors have size N (=1024) Done for all c[i]?

e into base Bg (=128) For each vector of decomposed values: log(Bg)(Q) times (=4)

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
