axytho/FHEWHW/sources_1/new/INTT.v

/*
Copyright 2020, Ahmet Can Mert <ahmetcanmert@sabanciuniv.edu>
edited for use in FHEW by Jonas Bertels <jonas.bertels@kuleuven.be>

Licensed under the Apache License, Version 2.0 (the "License");
you may not use this file except in compliance with the License.
You may obtain a copy of the License at

   http://www.apache.org/licenses/LICENSE-2.0

Unless required by applicable law or agreed to in writing, software
distributed under the License is distributed on an "AS IS" BASIS,
WITHOUT WARRANTIES OR CONDITIONS OF ANY KIND, either express or implied.
See the License for the specific language governing permissions and
limitations under the License.
*/

`include "defines.v"

// start: HIGH for 1 cc (after 1 cc, data starts going in)
// done : HIGH for 1 cc (after 1 cc, data starts going out)

// Input: standard order
// output: scrambled order

// --- Baseline Version
// * address bit-lengts are set according to worst-case
// * supports up-to 2^15-pt NTT/INTT
// * integer multiplier is not optimized
// * modular reduction is not optimized
// * wait state is not optimized

module INTT   (input                           clk,reset,
               input                           load_bram, //loads from 64 27 bit wires
               input                           start_full,//## runs bitreverse/intt/bitreverse
               input                           load_data,//loads from single wire
               input                           start_intt,// run intt/bitreverse
               input [`DATA_SIZE_ARB-1:0]      din,// single input
               input  [(2*`DATA_SIZE_ARB * `PE_NUMBER)-1:0] bramIn, //large input
               input                           output_data_single, //trigers single output of data
               input                           jState, //allows us to determine which input we use.
               output reg                      done, //done, triggered when writing away in 64 27 bit values
               output reg [(2*`DATA_SIZE_ARB *`PE_NUMBER)-1:0] inttOut,//###
               output reg [`DATA_SIZE_ARB-1:0]                      dout//for single output at the end
               // ###output reg [`DATA_SIZE_ARB-1:0] dout
               );
// ---------------------------------------------------------------- connections

//HARDCODE
wire start;
assign start = 0;

// parameters & control
reg [2:0] state;
// 0: IDLE
// 1: load twiddle factors + q + n_inv
// 2: load data
// 3: performs ntt
// 4: output data
// 5: last stage of intt

reg [`RING_DEPTH+3:0] sys_cntr;
wire [(4 *`PE_NUMBER)-1:0] write_addr_intt;

reg [`DATA_SIZE_ARB-1:0]q;
reg [`DATA_SIZE_ARB-1:0]n_inv;

// data tw brams (datain,dataout,waddr,raddr,wen)
reg [`DATA_SIZE_ARB-1:0]        pi [(2*`PE_NUMBER)-1:0];
wire[`DATA_SIZE_ARB-1:0]        po [(2*`PE_NUMBER)-1:0];
reg [`RING_DEPTH-`PE_DEPTH+1:0] pw [(2*`PE_NUMBER)-1:0];
reg [`RING_DEPTH-`PE_DEPTH+1:0] pr [(2*`PE_NUMBER)-1:0];
reg [0:0]                       pe [(2*`PE_NUMBER)-1:0];

reg [`DATA_SIZE_ARB-1:0]        ti [`PE_NUMBER-1:0];
wire[`DATA_SIZE_ARB-1:0]        to [`PE_NUMBER-1:0];
reg [`RING_DEPTH-`PE_DEPTH+3:0] tw [`PE_NUMBER-1:0];
reg [`RING_DEPTH-`PE_DEPTH+3:0] tr [`PE_NUMBER-1:0];
reg [0:0]                       te [`PE_NUMBER-1:0];

// control signals
wire [`RING_DEPTH-`PE_DEPTH+1:0]      raddr;
wire [`RING_DEPTH-`PE_DEPTH+1:0]      waddr0,waddr1;
wire                                  wen0  ,wen1  ;
wire                                  brsel0,brsel1;
wire                                  brselen0,brselen1;
wire [2*`PE_NUMBER*(`PE_DEPTH+1)-1:0] brscramble;
wire [`RING_DEPTH-`PE_DEPTH+2:0]      raddr_tw;

wire [4:0]                       stage_count;
wire                             ntt_finished;

reg                              do_full; 
wire                             jState1_and_first_reverse;
wire                             start_address_gen;

// pu
reg [`DATA_SIZE_ARB-1:0] NTTin [(2*`PE_NUMBER)-1:0];
reg [`DATA_SIZE_ARB-1:0] MULin [`PE_NUMBER-1:0];
wire[`DATA_SIZE_ARB-1:0] ASout [(2*`PE_NUMBER)-1:0]; // ADD-SUB out  (no extra delay after odd)
wire[`DATA_SIZE_ARB-1:0] EOout [(2*`PE_NUMBER)-1:0]; // EVEN-ODD out

reg [(`DATA_SIZE_ARB *`PE_NUMBER)-1:0] bramOut;
wire [(`PE_NUMBER *`PE_NUMBER)-1:0] reversed_input;
wire [(`DATA_SIZE_ARB *`PE_NUMBER)-1:0] bram_in_from_reversed;

// ---------------------------------------------------------------- BRAMs
// 2*PE BRAMs for input-output polynomial
// PE BRAMs for storing twiddle factors

generate
	genvar k;

    for(k=0; k<`PE_NUMBER ;k=k+1) begin: BRAM_GEN_BLOCK
        BRAM #(.DLEN(`DATA_SIZE_ARB),.HLEN(`RING_DEPTH-`PE_DEPTH+2)) bd00(clk,pe[2*k+0],pw[2*k+0],pi[2*k+0],pr[2*k+0],po[2*k+0]);
        BRAM #(.DLEN(`DATA_SIZE_ARB),.HLEN(`RING_DEPTH-`PE_DEPTH+2)) bd01(clk,pe[2*k+1],pw[2*k+1],pi[2*k+1],pr[2*k+1],po[2*k+1]);
        //###BRAM #(.DLEN(`DATA_SIZE_ARB),.HLEN(`RING_DEPTH-`PE_DEPTH+4)) bt00(clk,te[k],tw[k],ti[k],tr[k],to[k]);
        WINVSTORAGE #(.DLEN(`DATA_SIZE_ARB),.HLEN(`RING_DEPTH-`PE_DEPTH+4), .PE_NO(k)) bt00(clk,tr[k],to[k]);
    end
endgenerate

// ---------------------------------------------------------------- NTT2 units

generate
	genvar m;

    for(m=0; m<`PE_NUMBER ;m=m+1) begin: NTT2_GEN_BLOCK
        NTT2 nttu(clk,reset,
                  q,
			      NTTin[2*m+0],NTTin[2*m+1],
				  MULin[m],
				  ASout[2*m+0],ASout[2*m+1],
				  EOout[2*m+0],EOout[2*m+1]);
    end
endgenerate

// ---------------------------------------------------------------- control unit

AddressGenerator ag(clk,reset,
                    (start_address_gen),
                    raddr,
                    waddr0,waddr1,
                    wen0  ,wen1  ,
                    brsel0,brsel1,
                    brselen0,brselen1,
                    brscramble,
                    raddr_tw,
                    stage_count,
                    ntt_finished
                    );

// ---------------------------------------------------------------- ntt/intt
reg [`DATA_SIZE_ARB-1:0] params    [0:6];
initial begin
	// params
	$readmemh("D:/Jonas/Documents/Huiswerk/KULeuven5/VerilogThesis/edt_zcu102/edt_zcu102.srcs/sources_1/imports/VerilogThesis/test/PARAM.txt"    , params);
end

always @(posedge clk  ) begin
    if(reset) begin
        do_full <= 0;
    end
    else begin
        if(state == 3'd3)//once we're in the execution, make sure we don't go back to execution
            do_full <= 0;
        else if(start_full)
            do_full <= 1;
        else
            do_full <= do_full;
    end
end

// Make sure that we read from the correct part before bitreversing (I know this is really confusing anyonereading through this)
// but basically for all 64 BRAM's I'm loading 32 values at the end of each addToAcao
// This saves me a couple of clock cycles, but most importantly,
// it's simpler than trying to keep half the stuff in the NTT, and then reading out twice
// and it makes outputting easier
assign jState1_and_first_reverse = (do_full) &  (jState);

// ---------------------------------------------------------------- state machine & sys_cntr

always @(posedge clk  ) begin
    if(reset) begin
        state <= 3'd0;
        sys_cntr <= 0;
    end
    else begin
        case(state)
        3'd0: begin // wait for command
            if (output_data_single)
                 state <= 3'd7;//read out single
            else if(load_bram)
                state <= 3'd1;//read x64
            else if(load_data)
                state <= 3'd2;//read single
            else if(start_intt & ~do_full)// first time we do it this way because we load them them in inversely.
            // seen in hindsight, this is a "premature" optimisation
            // but actually the real problem was that the need for a bitreversal wasn't appararent at first.
                state <= 3'd3;//execute
            else if(start_intt & do_full)
                state <= 3'd6;//bitReverse, then execute
            else
                state <= 3'd0;
            sys_cntr <= 0;
        end
        3'd1: begin //BRAM x64 readin
            if(sys_cntr == ((`RING_SIZE >>(`PE_DEPTH)) - 1)) begin//read in 32 cycles
                state <= 3'd0;                    
                sys_cntr <= 0;
            end
            else begin
                state <= 3'd1;
                sys_cntr <= sys_cntr + 1;
            end
        end
        3'd2: begin //only run at the start of addToACAP
            if(sys_cntr == (`RING_SIZE-1)) begin //because it takes 1024 cycles, so we really don't want to do this every time
                state <= 3'd0;
                sys_cntr <= 0;
            end
            else begin
                state <= 3'd2;
                sys_cntr <= sys_cntr + 1;
            end
        end
        3'd3: begin
            if(ntt_finished)
                state <= 3'd5;
            else
                state <= 3'd3;
            sys_cntr <= 0;
        end
        3'd4: begin// read out x64
            if(sys_cntr == ((`RING_SIZE >> (`PE_DEPTH+1)) + 1)) begin
                state <= 3'd0;
                sys_cntr <= 0;
            end
            else begin
                state <= 3'd4;
                sys_cntr <= sys_cntr + 1;
            end
        end
        3'd5: begin //multiply with 1/N
            if(sys_cntr == (((`RING_SIZE >> (`PE_DEPTH+1))<<1) + `INTMUL_DELAY+`MODRED_DELAY+`STAGE_DELAY)) begin
                state <= 3'd6;
                sys_cntr <= 0;
            end
            else begin
                state <= 3'd5;
                sys_cntr <= sys_cntr + 1;
            end
        end
        3'd6: begin //bitReverse
            if ((sys_cntr == ((`RING_SIZE >> (`PE_DEPTH)) + `BITREVERSE_DELAY)) & ~do_full) begin
                state <= 3'd4;//readout
                sys_cntr <= 0;
            end
            else if ((sys_cntr == ((`RING_SIZE >> (`PE_DEPTH)) + `BITREVERSE_DELAY)) & do_full)  begin
                state <= 3'd3;//execute
                sys_cntr <= 0;
            end
            else begin
                state <= 3'd6;
                sys_cntr <= sys_cntr + 1;
            end
        end
        3'd7: begin //read out the BRAM's in single file
            if(sys_cntr == ((`RING_SIZE<<1)+1)) begin
                state <= 3'd0;
                sys_cntr <= 0;
            end
            else begin
                state <= 3'd7;
                sys_cntr <= sys_cntr + 1;
            end
        end
        default: begin
            state <= 3'd0;
            sys_cntr <= 0;
        end
        endcase
    end
end

//For the stupid address generator: (replaces start_intt, which would else trigger for state==6
assign start_address_gen = (((sys_cntr == ((`RING_SIZE >> (`PE_DEPTH)) + `BITREVERSE_DELAY)) & do_full) & (state == 3'd6)) || ((start_intt & ~do_full) & (state == 3'd0));

// ---------------------------------------------------------------- load twiddle factor + q + n_inv & other operations

always @(posedge clk  ) begin: TW_BLOCK
    integer n;
    for(n=0; n < (`PE_NUMBER); n=n+1) begin: LOOP_1
        if(reset) begin
            te[n] <= 0;
            tw[n] <= 0;
            ti[n] <= 0;
            tr[n] <= 0;
        end
        else begin
      /*###      if((state == 3'd1) && (sys_cntr < ((((1<<(`RING_DEPTH-`PE_DEPTH))-1)+`PE_DEPTH)<<`PE_DEPTH))) begin // for (16+8+4+2+1+1+1+1+1+1 = 36  * PE elements)
            //i.e. for every stage in the thing
                te[n] <= (n == (sys_cntr & ((1 << `PE_DEPTH)-1)));//standard way of writing a value away to a certain n every clock cycle (not super efficient)
                tw[n][`RING_DEPTH-`PE_DEPTH+3]   <= 0;
                tw[n][`RING_DEPTH-`PE_DEPTH+2:0] <= (sys_cntr >> `PE_DEPTH); // for every BRAM, write one once every 32 clock cycles.
                ti[n] <= din;
                tr[n] <= 0;
            end// now we load the inverse twiddle factors
            else if((state == 3'd1) && (sys_cntr < (((((1<<(`RING_DEPTH-`PE_DEPTH))-1)+`PE_DEPTH)<<`PE_DEPTH)<<1))) begin //for the second half
                                //enable at (sys_cntr - 36 * 32)  mod 32 (which makes sense)
                te[n] <= (n == ((sys_cntr-((((1<<(`RING_DEPTH-`PE_DEPTH))-1)+`PE_DEPTH)<<`PE_DEPTH)) & ((1 << `PE_DEPTH)-1)));
                tw[n][`RING_DEPTH-`PE_DEPTH+3]   <= 1; //write the inverse adresses, and write them as (sys_cntr - 32*36) // 32
                tw[n][`RING_DEPTH-`PE_DEPTH+2:0] <= ((sys_cntr-((((1<<(`RING_DEPTH-`PE_DEPTH))-1)+`PE_DEPTH)<<`PE_DEPTH)) >> `PE_DEPTH);//so write once
                // every 32 clock cycles.
                ti[n] <= din;
                tr[n] <= 0;
            end */
            /*else */if(state == 3'd3) begin // NTT operations
                te[n] <= 0;
                tw[n] <= 0;
                ti[n] <= 0;
                tr[n] <= raddr_tw;
                //###tr[n] <= {ntt_intt,raddr_tw};// send it to EVERY PE (so how we write it in is simportant obviously)
            end
            else begin
                te[n] <= 0;
                tw[n] <= 0;
                ti[n] <= 0;
                tr[n] <= 0;
            end
        end
    end
end

always @(posedge clk  ) begin
    if(reset) begin
        q     <= 0;
        n_inv <= 0;
    end
    else begin
        q     <= params[1];
        n_inv <= params[6];
    end
end

// ---------------------------------------------------------------- load data & other data operations
// ### is the symbol for code that I write, and commented code will have a hashtag in from of it
wire [`RING_DEPTH-`PE_DEPTH-1:0] addrout;//allows us to do 32 addresses, which is what we want
assign addrout = (sys_cntr >> (`PE_DEPTH+1));//every 64 cycles, which is correct, even for twice the ammount of cycles

wire [`RING_DEPTH-`PE_DEPTH-1:0] inttlast;
assign inttlast = (sys_cntr & ((`RING_SIZE >> (`PE_DEPTH+1))-1)); //counter mod 16

wire [`RING_DEPTH-`PE_DEPTH-2:0] read_out_bram [(`PE_NUMBER<<1)-1:0];
generate
genvar n_bram;
for (n_bram = 0; n_bram < (2*`PE_NUMBER); n_bram= n_bram + 1) begin
    assign read_out_bram[n_bram] = ((n_bram[4:1]) + (inttlast[3:0])) & ((`RING_SIZE >> (`PE_DEPTH+1))-1);
end
endgenerate
generate
genvar t;
for (t=0; t<`PE_NUMBER; t=t+1) begin
   assign write_addr_intt[4*t+:4] = reversed_input[(`PE_NUMBER *(t+1) - 5)+:4];
   assign bram_in_from_reversed[(t*`DATA_SIZE_ARB)+:`DATA_SIZE_ARB] = reversed_input[(t*`PE_NUMBER)+:`DATA_SIZE_ARB];
end
endgenerate

wire [`RING_DEPTH-`PE_DEPTH-2:0] cycle_bitreverse;
assign cycle_bitreverse = inttlast[`RING_DEPTH-`PE_DEPTH-2:0] - 2'd2;

bitReverse reverser (
    clk, reset,
    cycle_bitreverse,
    bramOut,
    reversed_input
);

//###
reg [`RING_DEPTH-1:0] reverse_sys_cntr;
integer i;
//###
always @*
for(i=0;i<`RING_DEPTH;i=i+1)
    reverse_sys_cntr[i] = sys_cntr[`RING_DEPTH-i-1];

wire [`RING_DEPTH+3:0]           sys_cntr_d;
wire [`RING_DEPTH-`PE_DEPTH-1:0]           sys_cntr_bit_reverse_delayed;
wire [`RING_DEPTH-`PE_DEPTH-1:0] inttlast_d;


always @(posedge clk  ) begin: DT_BLOCK
    integer n;
    for(n=0; n < (2*`PE_NUMBER); n=n+1) begin: LOOP_1
        
        if(reset) begin
            pe[n] <= 0;
            pw[n] <= 0;
            pi[n] <= 0;
            pr[n] <= 0;
        end
        else begin
            
            
            if((state == 3'd1)) begin // input data from BRAM
                    // ###
                pe[n] <= 1'b1; //read everything fast
                pw[n] <= {2'b10, sys_cntr[4:0]};//inttlast is fake 5 bits, we need sys_cntr, which we need here.
                pi[n] <= bramIn[n*`DATA_SIZE_ARB+:`DATA_SIZE_ARB];
                pr[n] <= 0;
            end
        
        
            else if((state == 3'd2)) begin // input data
            // ###
                if(reverse_sys_cntr < (`RING_SIZE >> 1)) begin
                    pe[n] <= (n == ((reverse_sys_cntr & ((1 << `PE_DEPTH)-1)) << 1)); //only even n's
                    pw[n] <= (reverse_sys_cntr >> `PE_DEPTH); //write the first 512 values to these even n's (note that these are the BRAM0's.)
                    pi[n] <= din;
                    pr[n] <= 0;
                end
                else begin
                    pe[n] <= (n == (((reverse_sys_cntr & ((1 << `PE_DEPTH)-1)) << 1)+1));// only odd n's
                    pw[n] <= ((reverse_sys_cntr-(`RING_SIZE >> 1)) >> `PE_DEPTH);// write them to the BRAM1
                    pi[n] <= din;
                    pr[n] <= 0;
                end // ### 
            end
            else if(state == 3'd3) begin // NTT operations
            //writeback is split into 2 stages: in the first stage we write 
                if(stage_count < (`RING_DEPTH - `PE_DEPTH - 1)) begin
                    if(brselen0) begin
                        if(brsel0 == 0) begin
                            if(n[0] == 0) begin
                                pe[n] <= wen0;
                                pw[n] <= waddr0;
                                pi[n] <= EOout[n];
                            end
                        end
                        else begin // brsel0 == 1
                            if(n[0] == 0) begin
                                pe[n] <= wen1;
                                pw[n] <= waddr1;
                                pi[n] <= EOout[n+1];
                            end
                        end
                    end
                    else begin
                        if(n[0] == 0) begin
                            pe[n] <= 0;
                            pw[n] <= pw[n];
                            pi[n] <= pi[n];
                        end
                    end
                    if(brselen1) begin
                        if(brsel1 == 0) begin
                            if(n[0] == 1) begin
                                pe[n] <= wen0;
                                pw[n] <= waddr0;
                                pi[n] <= EOout[n-1];
                            end
                        end
                        else begin // brsel1 == 1
                            if(n[0] == 1) begin
                                pe[n] <= wen1;
                                pw[n] <= waddr1;
                                pi[n] <= EOout[n];
                            end
                        end
                    end
                    else begin
                        if(n[0] == 1) begin
                            pe[n] <= 0;
                            pw[n] <= pw[n];
                            pi[n] <= pi[n];
                        end
                    end
                end
                else if(stage_count < (`RING_DEPTH - 1)) begin
                    pe[n] <= wen0;
                    pw[n] <= waddr0;
                    pi[n] <= ASout[brscramble[(`PE_DEPTH+1)*n+:(`PE_DEPTH+1)]];
                end
                else begin// this is what you're going to want: when stage_cout == RING_DEPTH -1
                    pe[n] <= wen0;
                    pw[n] <= waddr0;
                    pi[n] <= ASout[n];
                end
                pr[n] <= raddr;
            end
            
            
            
            else if(state == 3'd4) begin // output to
                pe[n] <= 0;
                pw[n] <= 0;
                pi[n] <= 0;
                //###pr[n] <= {2'b10,addrout};
                pr[n] <= {2'b00, inttlast}; //this outputs where bitreverse stored it
                //OVER HERE!!!!
            end
            

            
            
            
            
            else if(state == 3'd5) begin // last stage of intt
                if(sys_cntr_d < (`RING_SIZE >> (`PE_DEPTH+1))) begin
                    if(n[0] == 0) begin
                        pe[n] <= 1;
                        pw[n] <= {2'b10,inttlast_d};
                        pi[n] <= ASout[n+1];
                    end
                    else begin
                        pe[n] <= 0;
                        pw[n] <= 0;
                        pi[n] <= 0;
                    end
                end
                else if(sys_cntr_d < (`RING_SIZE >> (`PE_DEPTH))) begin
                    if(n[0] == 1) begin
                        pe[n] <= 1;
                        pw[n] <= {2'b10,inttlast_d};
                        pi[n] <= ASout[n];
                    end
                    else begin
                        pe[n] <= 0;
                        pw[n] <= 0;
                        pi[n] <= 0;
                    end
                end
                
                else begin
                    pe[n] <= 0;
                    pw[n] <= 0;
                    pi[n] <= 0;
                end
                pr[n] <= {2'b10,inttlast};
            end
            
            
            else if((state == 3'd6)) begin
                pr[n] <= {2'b10,jState1_and_first_reverse, read_out_bram[n]};//read_out_bram is always 4 bits
                if ((sys_cntr < `BITREVERSE_DELAY)) begin // input data from reverser
                    // ###
                    pe[n] <= 0; //first 0,1, 4,5, 8,9, etc...
                    pw[n] <= 0; //write to 00 from 10
                    pi[n] <= 0;
                    
                end
                else begin
                    pe[n] <= (n[0] == sys_cntr_bit_reverse_delayed[4]); //first 0,2, 4,6, 8,10, etc...
                    pw[n] <= write_addr_intt[4*n[5:1]+:4]; //write to 00 from 10
                    pi[n] <= bram_in_from_reversed[n[5:1]*`DATA_SIZE_ARB+:`DATA_SIZE_ARB];
                end
            end
            else if(state == 3'd7) begin // output data
                pe[n] <= 0;
                pw[n] <= 0;
                pi[n] <= 0;
                pr[n] <= {2'b10,sys_cntr[(`RING_DEPTH):(`RING_DEPTH-`PE_DEPTH+1)]};//replaces addrout
            end
            else begin
                pe[n] <= 0;
                pw[n] <= 0;
                pi[n] <= 0;
                pr[n] <= 0;
            end
        end
    end
end

// done signal & output data
wire [`PE_DEPTH:0] coefout;
assign coefout = (sys_cntr-2);

always @(*) begin: REVERSE_BLOCK
integer n;
    for(n=0; n < (`PE_NUMBER); n=n+1) begin: LOOP_1
        if(reset) begin
            bramOut <= 0;
        end
        else begin
            if(state == 3'd6 && sys_cntr > 1) begin//there are 2 parts to this state
                if (sys_cntr < (`PE_NUMBER >> 1) + 2) begin
                    bramOut[(`DATA_SIZE_ARB)*n+:(`DATA_SIZE_ARB)] <= po[n<< 1];//first even PE's
                end else begin
                    bramOut[(`DATA_SIZE_ARB)*n+:(`DATA_SIZE_ARB)] <= po[(n<< 1) + 1];//then odd PE's
                end
                //then the others
            end
            else begin
                bramOut <= 0;
            end
        end
    end
end



always @(posedge clk  ) begin: OUT_BLOCK
integer n;
    for(n=0; n < (2*`PE_NUMBER); n=n+1) begin: LOOP_1
        if(reset) begin
            done <= 0;
            inttOut <= 0;
        end
        else begin
            if(state == 3'd4) begin//TODO: DELAY inttOut by 2, because memory and stuff
                done <= (sys_cntr == 1); // we do not OUTPUT done when we are explicitly asked for output.
                inttOut[(`DATA_SIZE_ARB)*n+:(`DATA_SIZE_ARB)] <= po[n];

                //then the others
            end
            else begin
                done <= 0;
                inttOut <= 0;
            end
        end
    end
end
always @(posedge clk  ) begin
    if(reset) begin
        dout <= 0;
    end
    else begin
        if(state == 3'd7) begin
            dout <= po[coefout];
        end
        else begin
            dout <= 0;
        end
    end
end
// ---------------------------------------------------------------- PU control

always @(posedge clk  ) begin: NT_BLOCK
    integer n;
    for(n=0; n < (`PE_NUMBER); n=n+1) begin: LOOP_1
        if(reset) begin
            NTTin[2*n+0] <= 0;
            NTTin[2*n+1] <= 0;
            MULin[n] <= 0;
        end
        else begin
            if(state == 3'd5) begin //If we're doing the multiplication with 1/N
                if(sys_cntr < (2+(`RING_SIZE >> (`PE_DEPTH+1)))) begin // should take 2 + 16 cycles to read everything and write it back with
                // 1 delay.
                    NTTin[2*n+0] <= po[2*n+0];
                    NTTin[2*n+1] <= 0;
                end
                else if(sys_cntr < (2+(`RING_SIZE >> (`PE_DEPTH)))) begin
                    NTTin[2*n+0] <= po[2*n+1];
                    NTTin[2*n+1] <= 0;
                end
                else begin //again, this is the standard operation
                    NTTin[2*n+0] <= po[2*n+0];
                    NTTin[2*n+1] <= po[2*n+1];
                end
                MULin[n] <= n_inv;
            end
            else begin //standard operation, mainly in state 3.
                NTTin[2*n+0] <= po[2*n+0];
                NTTin[2*n+1] <= po[2*n+1];
                MULin[n] <= to[n];
            end
        end
    end
end

// --------------------------------------------------------------------------- delays
ShiftReg #(.SHIFT(`BITREVERSE_DELAY+1),.DATA(`RING_DEPTH-`PE_DEPTH)) sr02(clk,reset,sys_cntr[`RING_DEPTH-`PE_DEPTH-1:0],sys_cntr_bit_reverse_delayed);
ShiftReg #(.SHIFT(`INTMUL_DELAY+`MODRED_DELAY+`STAGE_DELAY-1),.DATA(`RING_DEPTH+4        )) sr00(clk,reset,sys_cntr,sys_cntr_d);
ShiftReg #(.SHIFT(`INTMUL_DELAY+`MODRED_DELAY+`STAGE_DELAY-1),.DATA(`RING_DEPTH-`PE_DEPTH)) sr01(clk,reset,inttlast,inttlast_d);

// ---------------------------------------------------------------------------

endmodule
