axytho/FHEWHW/sources_1/new/WINVSTORAGE.v

/*
Copyright 2020, Ahmet Can Mert <ahmetcanmert@sabanciuniv.edu>

Licensed under the Apache License, Version 2.0 (the "License");
you may not use this file except in compliance with the License.
You may obtain a copy of the License at

   http://www.apache.org/licenses/LICENSE-2.0

Unless required by applicable law or agreed to in writing, software
distributed under the License is distributed on an "AS IS" BASIS,
WITHOUT WARRANTIES OR CONDITIONS OF ANY KIND, either express or implied.
See the License for the specific language governing permissions and
limitations under the License.
*/
`include "defines.v"


module WINVSTORAGE #(parameter DLEN = 32, HLEN = 9, PE_NO=0)
           (input                 clk,
            input      [HLEN-1:0] raddr,
            output reg [DLEN-1:0] dout);
// bram
// if you want storage for the secret key, write "distributed" see the BRAM help files.
// try synthesizing the entire secret key storage.


(* ram_style="auto" *) reg [DLEN-1:0] blockram [(((1<<(`RING_DEPTH-`PE_DEPTH))-1)+`PE_DEPTH)-1:0];//this is the default
generate
initial begin
//NOT SO FAST, NEEDS TO BE DONE SEPERATELY BECAUSE SEPERATE BRAMS
// SO YOURE GOING TO HAVE TO MAKE THE W FILES INDIVIDUALLY IF YOU WANT TO DO THIS
    case(PE_NO)
        0 : $readmemh("D:/Jonas/Documents/Huiswerk/KULeuven5/VerilogThesis/edt_zcu102/edt_zcu102.srcs/sources_1/imports/VerilogThesis/test/WINV_0.txt",  blockram);
    1 : $readmemh("D:/Jonas/Documents/Huiswerk/KULeuven5/VerilogThesis/edt_zcu102/edt_zcu102.srcs/sources_1/imports/VerilogThesis/test/WINV_1.txt",  blockram);
    2 : $readmemh("D:/Jonas/Documents/Huiswerk/KULeuven5/VerilogThesis/edt_zcu102/edt_zcu102.srcs/sources_1/imports/VerilogThesis/test/WINV_2.txt",  blockram);
    3 : $readmemh("D:/Jonas/Documents/Huiswerk/KULeuven5/VerilogThesis/edt_zcu102/edt_zcu102.srcs/sources_1/imports/VerilogThesis/test/WINV_3.txt",  blockram);
    4 : $readmemh("D:/Jonas/Documents/Huiswerk/KULeuven5/VerilogThesis/edt_zcu102/edt_zcu102.srcs/sources_1/imports/VerilogThesis/test/WINV_4.txt",  blockram);
    5 : $readmemh("D:/Jonas/Documents/Huiswerk/KULeuven5/VerilogThesis/edt_zcu102/edt_zcu102.srcs/sources_1/imports/VerilogThesis/test/WINV_5.txt",  blockram);
    6 : $readmemh("D:/Jonas/Documents/Huiswerk/KULeuven5/VerilogThesis/edt_zcu102/edt_zcu102.srcs/sources_1/imports/VerilogThesis/test/WINV_6.txt",  blockram);
    7 : $readmemh("D:/Jonas/Documents/Huiswerk/KULeuven5/VerilogThesis/edt_zcu102/edt_zcu102.srcs/sources_1/imports/VerilogThesis/test/WINV_7.txt",  blockram);
    8 : $readmemh("D:/Jonas/Documents/Huiswerk/KULeuven5/VerilogThesis/edt_zcu102/edt_zcu102.srcs/sources_1/imports/VerilogThesis/test/WINV_8.txt",  blockram);
    9 : $readmemh("D:/Jonas/Documents/Huiswerk/KULeuven5/VerilogThesis/edt_zcu102/edt_zcu102.srcs/sources_1/imports/VerilogThesis/test/WINV_9.txt",  blockram);
    10 : $readmemh("D:/Jonas/Documents/Huiswerk/KULeuven5/VerilogThesis/edt_zcu102/edt_zcu102.srcs/sources_1/imports/VerilogThesis/test/WINV_10.txt",  blockram);
    11 : $readmemh("D:/Jonas/Documents/Huiswerk/KULeuven5/VerilogThesis/edt_zcu102/edt_zcu102.srcs/sources_1/imports/VerilogThesis/test/WINV_11.txt",  blockram);
    12 : $readmemh("D:/Jonas/Documents/Huiswerk/KULeuven5/VerilogThesis/edt_zcu102/edt_zcu102.srcs/sources_1/imports/VerilogThesis/test/WINV_12.txt",  blockram);
    13 : $readmemh("D:/Jonas/Documents/Huiswerk/KULeuven5/VerilogThesis/edt_zcu102/edt_zcu102.srcs/sources_1/imports/VerilogThesis/test/WINV_13.txt",  blockram);
    14 : $readmemh("D:/Jonas/Documents/Huiswerk/KULeuven5/VerilogThesis/edt_zcu102/edt_zcu102.srcs/sources_1/imports/VerilogThesis/test/WINV_14.txt",  blockram);
    15 : $readmemh("D:/Jonas/Documents/Huiswerk/KULeuven5/VerilogThesis/edt_zcu102/edt_zcu102.srcs/sources_1/imports/VerilogThesis/test/WINV_15.txt",  blockram);
    16 : $readmemh("D:/Jonas/Documents/Huiswerk/KULeuven5/VerilogThesis/edt_zcu102/edt_zcu102.srcs/sources_1/imports/VerilogThesis/test/WINV_16.txt",  blockram);
    17 : $readmemh("D:/Jonas/Documents/Huiswerk/KULeuven5/VerilogThesis/edt_zcu102/edt_zcu102.srcs/sources_1/imports/VerilogThesis/test/WINV_17.txt",  blockram);
    18 : $readmemh("D:/Jonas/Documents/Huiswerk/KULeuven5/VerilogThesis/edt_zcu102/edt_zcu102.srcs/sources_1/imports/VerilogThesis/test/WINV_18.txt",  blockram);
    19 : $readmemh("D:/Jonas/Documents/Huiswerk/KULeuven5/VerilogThesis/edt_zcu102/edt_zcu102.srcs/sources_1/imports/VerilogThesis/test/WINV_19.txt",  blockram);
    20 : $readmemh("D:/Jonas/Documents/Huiswerk/KULeuven5/VerilogThesis/edt_zcu102/edt_zcu102.srcs/sources_1/imports/VerilogThesis/test/WINV_20.txt",  blockram);
    21 : $readmemh("D:/Jonas/Documents/Huiswerk/KULeuven5/VerilogThesis/edt_zcu102/edt_zcu102.srcs/sources_1/imports/VerilogThesis/test/WINV_21.txt",  blockram);
    22 : $readmemh("D:/Jonas/Documents/Huiswerk/KULeuven5/VerilogThesis/edt_zcu102/edt_zcu102.srcs/sources_1/imports/VerilogThesis/test/WINV_22.txt",  blockram);
    23 : $readmemh("D:/Jonas/Documents/Huiswerk/KULeuven5/VerilogThesis/edt_zcu102/edt_zcu102.srcs/sources_1/imports/VerilogThesis/test/WINV_23.txt",  blockram);
    24 : $readmemh("D:/Jonas/Documents/Huiswerk/KULeuven5/VerilogThesis/edt_zcu102/edt_zcu102.srcs/sources_1/imports/VerilogThesis/test/WINV_24.txt",  blockram);
    25 : $readmemh("D:/Jonas/Documents/Huiswerk/KULeuven5/VerilogThesis/edt_zcu102/edt_zcu102.srcs/sources_1/imports/VerilogThesis/test/WINV_25.txt",  blockram);
    26 : $readmemh("D:/Jonas/Documents/Huiswerk/KULeuven5/VerilogThesis/edt_zcu102/edt_zcu102.srcs/sources_1/imports/VerilogThesis/test/WINV_26.txt",  blockram);
    27 : $readmemh("D:/Jonas/Documents/Huiswerk/KULeuven5/VerilogThesis/edt_zcu102/edt_zcu102.srcs/sources_1/imports/VerilogThesis/test/WINV_27.txt",  blockram);
    28 : $readmemh("D:/Jonas/Documents/Huiswerk/KULeuven5/VerilogThesis/edt_zcu102/edt_zcu102.srcs/sources_1/imports/VerilogThesis/test/WINV_28.txt",  blockram);
    29 : $readmemh("D:/Jonas/Documents/Huiswerk/KULeuven5/VerilogThesis/edt_zcu102/edt_zcu102.srcs/sources_1/imports/VerilogThesis/test/WINV_29.txt",  blockram);
    30 : $readmemh("D:/Jonas/Documents/Huiswerk/KULeuven5/VerilogThesis/edt_zcu102/edt_zcu102.srcs/sources_1/imports/VerilogThesis/test/WINV_30.txt",  blockram);
    31 : $readmemh("D:/Jonas/Documents/Huiswerk/KULeuven5/VerilogThesis/edt_zcu102/edt_zcu102.srcs/sources_1/imports/VerilogThesis/test/WINV_31.txt",  blockram);
    
        //(1<<HLEN)-1
        //((((1<<(`RING_DEPTH-`PE_DEPTH))-1)+`PE_DEPTH)<<`PE_DEPTH)-1
    endcase    

end
endgenerate

// read operation
always @(posedge clk) begin
    dout <= blockram[raddr];
end

endmodule
