axytho/FHEWHW/twiddleFactorGeneration/NTTN_test.v

/*
Copyright 2020, Ahmet Can Mert <ahmetcanmert@sabanciuniv.edu>

Licensed under the Apache License, Version 2.0 (the "License");
you may not use this file except in compliance with the License.
You may obtain a copy of the License at

   http://www.apache.org/licenses/LICENSE-2.0

Unless required by applicable law or agreed to in writing, software
distributed under the License is distributed on an "AS IS" BASIS,
WITHOUT WARRANTIES OR CONDITIONS OF ANY KIND, either express or implied.
See the License for the specific language governing permissions and
limitations under the License.
*/

`include "defines.v"

module NTTN_test();

parameter HP = 5;
parameter FP = (2*HP);

reg                       clk,reset;
reg                       load_w;
reg                       load_data;
reg                       start;
reg                       start_intt;
reg  [`DATA_SIZE_ARB-1:0] din;
wire                      done;
wire [`DATA_SIZE_ARB-1:0] dout;

// ---------------------------------------------------------------- CLK

always #HP clk = ~clk;

// ---------------------------------------------------------------- TXT data

reg [`DATA_SIZE_ARB-1:0] params    [0:7];
reg [`DATA_SIZE_ARB-1:0] w	 	   [0:((((1<<(`RING_DEPTH-`PE_DEPTH))-1)+`PE_DEPTH)<<`PE_DEPTH)-1];
reg [`DATA_SIZE_ARB-1:0] winv	   [0:((((1<<(`RING_DEPTH-`PE_DEPTH))-1)+`PE_DEPTH)<<`PE_DEPTH)-1];
reg [`DATA_SIZE_ARB-1:0] ntt_pin   [0:`RING_SIZE-1];
reg [`DATA_SIZE_ARB-1:0] ntt_pout  [0:`RING_SIZE-1];
reg [`DATA_SIZE_ARB-1:0] intt_pin  [0:`RING_SIZE-1];
reg [`DATA_SIZE_ARB-1:0] intt_pout [0:`RING_SIZE-1];

initial begin
	// ntt
	$readmemh("test/PARAM.txt"    , params);
	$readmemh("test/W.txt"        , w);
	$readmemh("test/WINV.txt"     , winv);
	$readmemh("test/NTT_DIN.txt"  , ntt_pin);
	$readmemh("test/NTT_DOUT.txt" , ntt_pout);
	$readmemh("test/INTT_DIN.txt" , intt_pin);
	$readmemh("test/INTT_DOUT.txt", intt_pout);
end

// ---------------------------------------------------------------- TEST case

integer k;

initial begin: CLK_RESET_INIT
	// clk & reset (150 cc)
	clk       = 0;
	reset     = 0;

	#200;
	reset    = 1;
	#200;
	reset    = 0;
	#100;

	#1000;
end

initial begin: LOAD_DATA
    load_w    = 0;
    load_data = 0;
    start     = 0;
    start_intt= 0;
    din       = 0;

    #1500;

    // load w
    load_w = 1;
    #FP;
    load_w = 0;

	for(k=0; k<((((1<<(`RING_DEPTH-`PE_DEPTH))-1)+`PE_DEPTH)<<`PE_DEPTH); k=k+1) begin
		din = w[k];
		#FP;
	end
	for(k=0; k<((((1<<(`RING_DEPTH-`PE_DEPTH))-1)+`PE_DEPTH)<<`PE_DEPTH); k=k+1) begin
		din = winv[k];
		#FP;
	end
	din = params[1];
	#FP;
	din = params[6];
	#FP;

	#(5*FP);

	// ---------- load data (ntt)
	load_data = 1;
    #FP;
    load_data = 0;

	for(k=0; k<(`RING_SIZE); k=k+1) begin
		din = ntt_pin[k];
		#FP;
	end

	#(5*FP);

	// start (ntt)
	start = 1;
	#FP;
	start = 0;
	#FP;

	while(done == 0)
		#FP;
	#FP;

	#(FP*(`RING_SIZE+10))

	// ---------- load data (intt)
	load_data = 1;
    #FP;
    load_data = 0;

	for(k=0; k<(`RING_SIZE); k=k+1) begin
		din = intt_pin[k];
		#FP;
	end

	#(5*FP);

	// start (ntt)
	start_intt = 1;
	#FP;
	start_intt = 0;
	#FP;

	while(done == 0)
		#FP;
	#FP;

	#(FP*(`RING_SIZE+10));

end

// ---------------------------------------------------------------- TEST control

reg [`DATA_SIZE_ARB-1:0] ntt_nout  [0:`RING_SIZE-1];
reg [`DATA_SIZE_ARB-1:0] intt_nout [0:`RING_SIZE-1];

integer m;
integer en,ei;

initial begin: CHECK_RESULT
	en = 0;
	ei = 0;
    #1500;

	// wait result (ntt)
	while(done == 0)
		#FP;
	#FP;

	// Store output (ntt)
	for(m=0; m<(`RING_SIZE); m=m+1) begin
		ntt_nout[m] = dout;
		#FP;
	end

	#FP;

	// wait result (intt)
	while(done == 0)
		#FP;
	#FP;

	// Store output (intt)
	for(m=0; m<(`RING_SIZE); m=m+1) begin
		intt_nout[m] = dout;
		#FP;
	end

	// Compare output with expected result (ntt)
	for(m=0; m<(`RING_SIZE); m=m+1) begin
		if(ntt_nout[m] == ntt_pout[m]) begin
			en = en+1;
		end
		else begin
		    $display("NTT:  Index-%d -- Calculated:%d, Expected:%d",m,ntt_nout[m],ntt_pout[m]);
		end
	end

	// Compare output with expected result (intt)
	for(m=0; m<(`RING_SIZE); m=m+1) begin
		if(intt_nout[m] == intt_pout[m]) begin
			ei = ei+1;
		end
		else begin
		    $display("INTT: Index-%d -- Calculated:%d, Expected:%d",m,intt_nout[m],intt_pout[m]);
		end
	end

	#FP;

	if(en == (`RING_SIZE))
		$display("NTT:  Correct");
	else
		$display("NTT:  Incorrect");

	if(ei == (`RING_SIZE))
		$display("INTT: Correct");
	else
		$display("INTT: Incorrect");

	$stop();

end

// ---------------------------------------------------------------- UUT

NTTN uut    (clk,reset,
             load_w,
             load_data,
             start,
             start_intt,
             din,
             done,
             dout);

endmodule
